pulcher/secureMoodTracker/Assests/20190905_112706.jpg

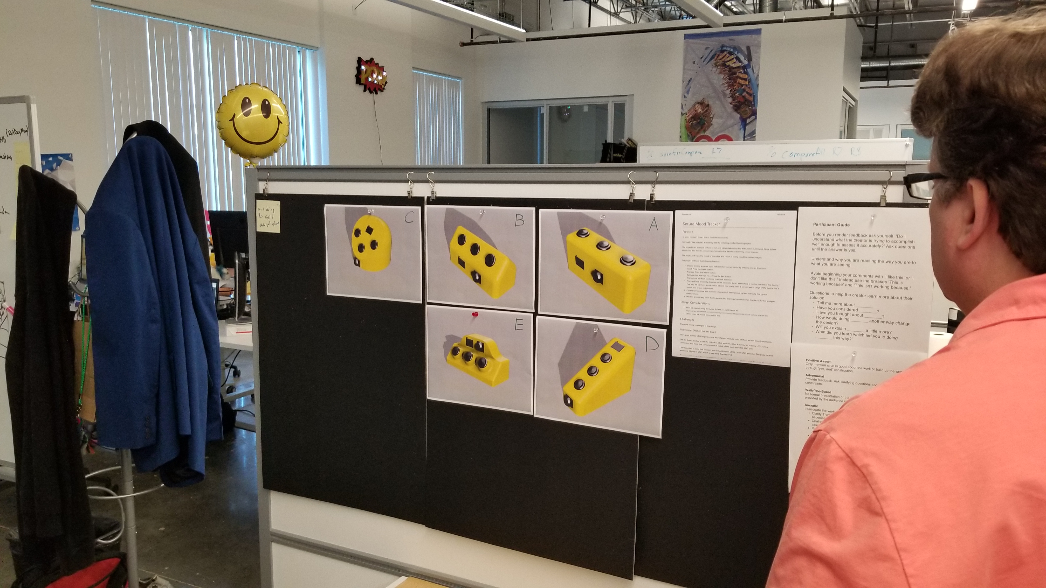
Assests/20190905_112706.jpg
