pulcher/secureMoodTracker/Assests/20190905_112857.jpg

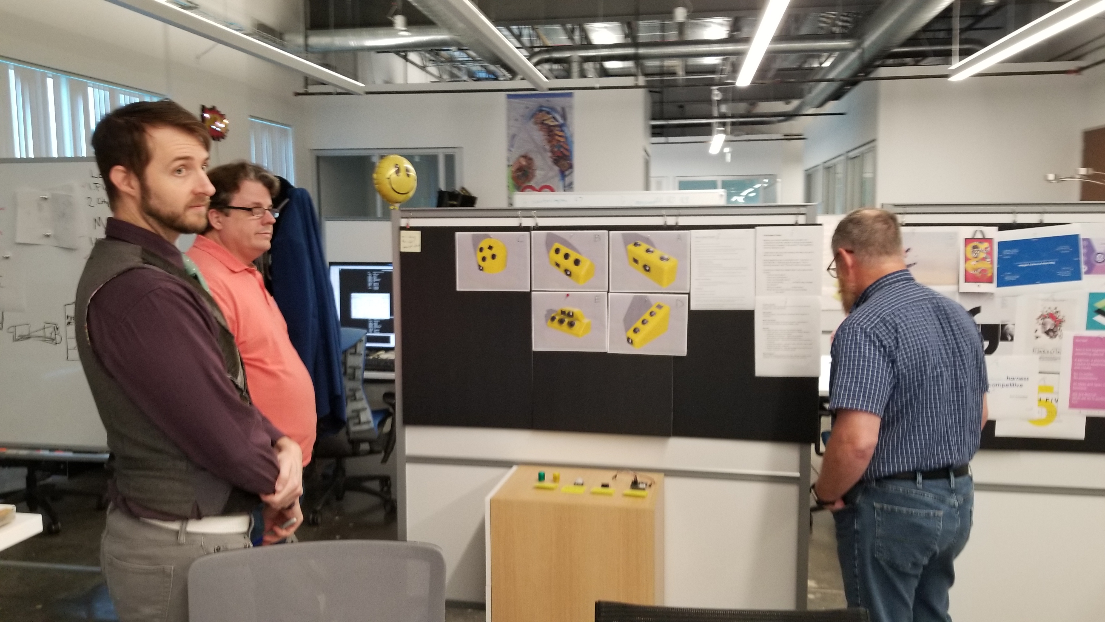
Assests/20190905_112857.jpg
