pulcher/secureMoodTracker/Assests/20190905_112900.jpg

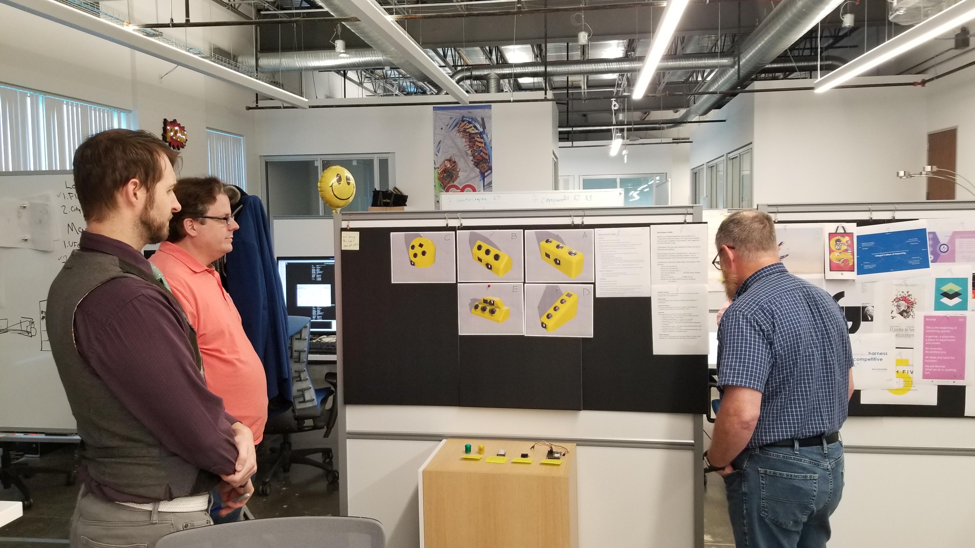
Assests/20190905_112900.jpg
