pulcher/secureMoodTracker/Assests/access-token-copy-token.jpg

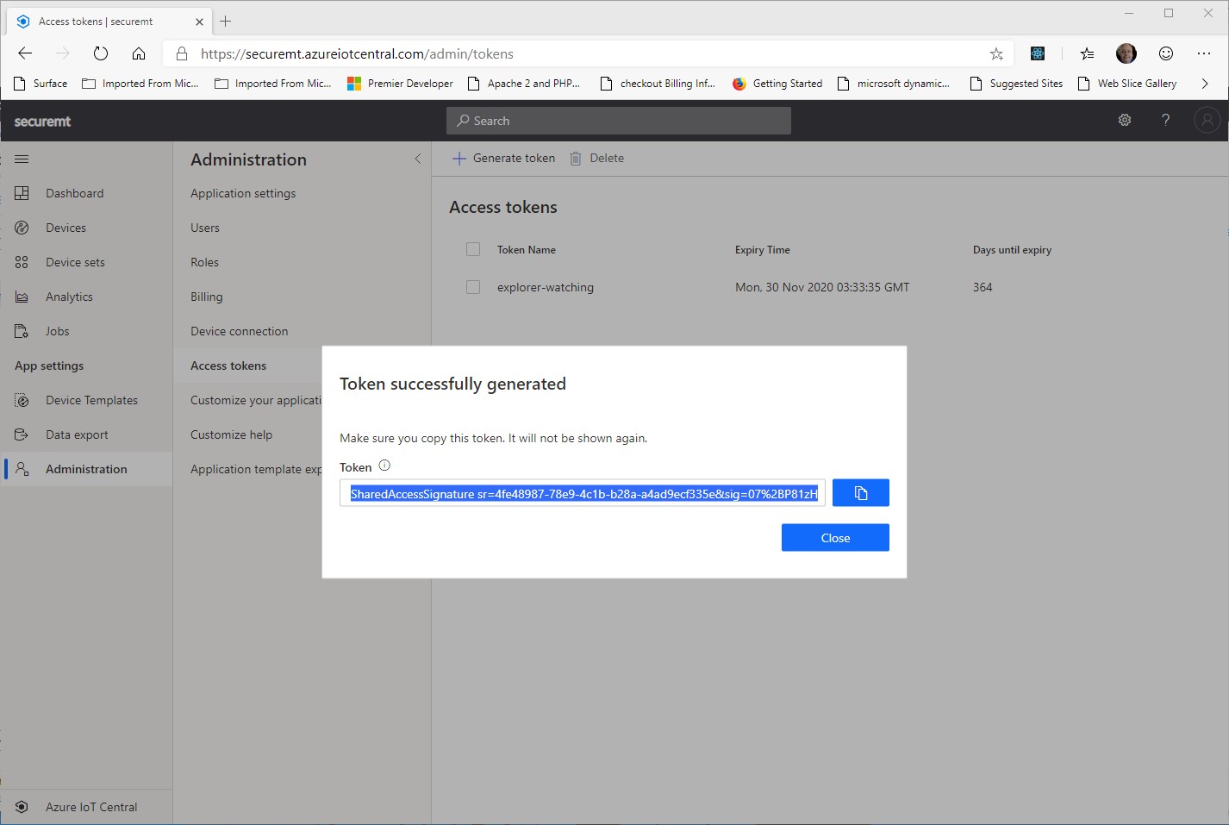
Assests/access-token-copy-token.jpg
