pulcher/secureMoodTracker/Assests/access-token-using-token.jpg

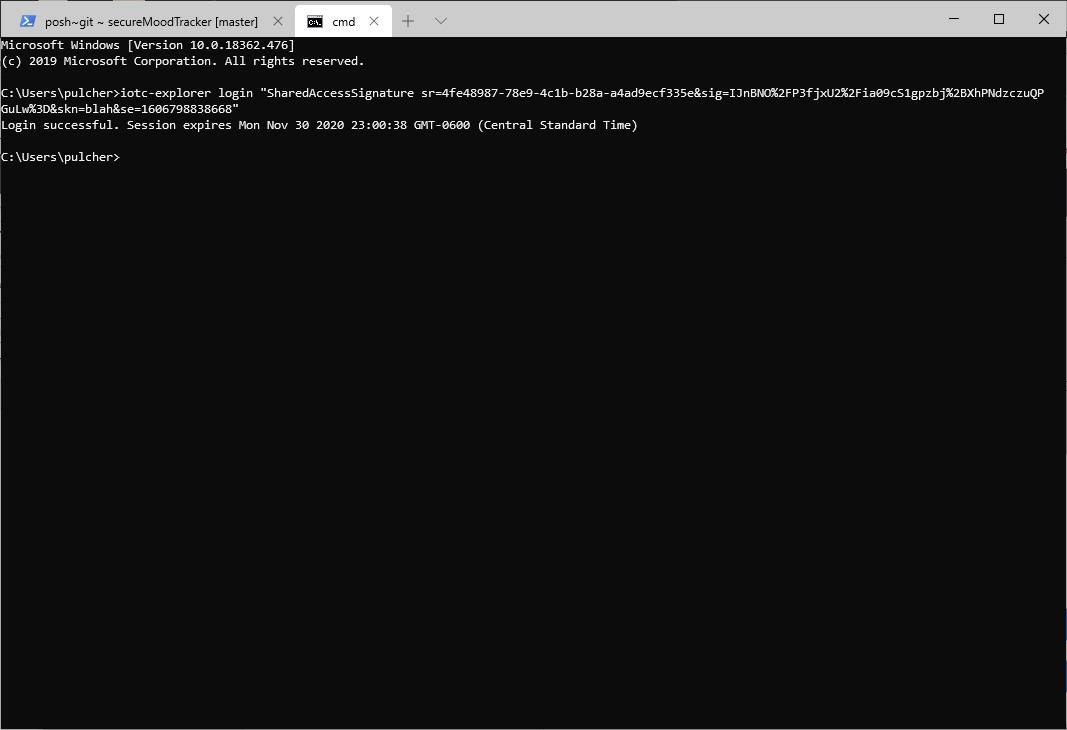
Assests/access-token-using-token.jpg
