pulcher/secureMoodTracker/Assests/adafruit mini arcade button v4.png

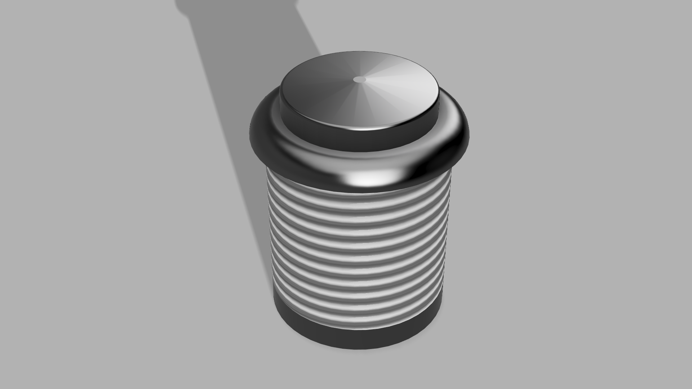
Assests/adafruit mini arcade button v4.png
