pulcher/secureMoodTracker/Assests/azsphere-login.jpg

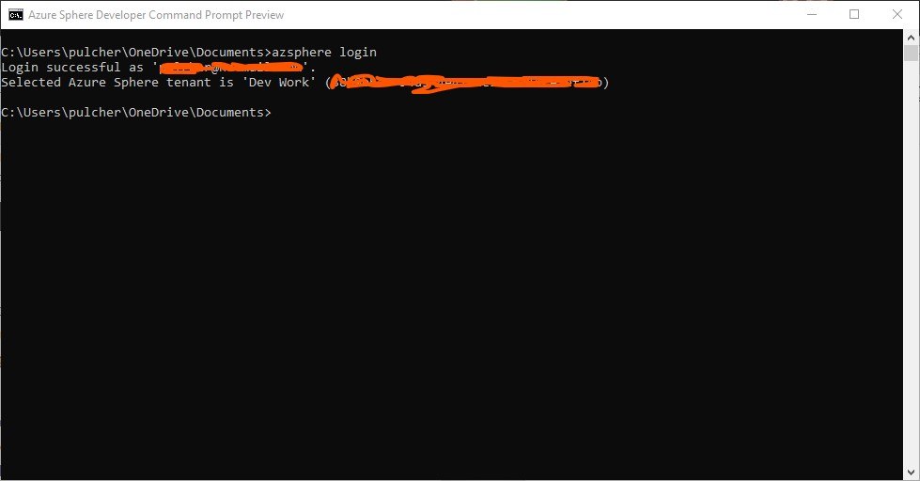
Assests/azsphere-login.jpg
