pulcher/secureMoodTracker/Assests/azsphere-show-attached.jpg

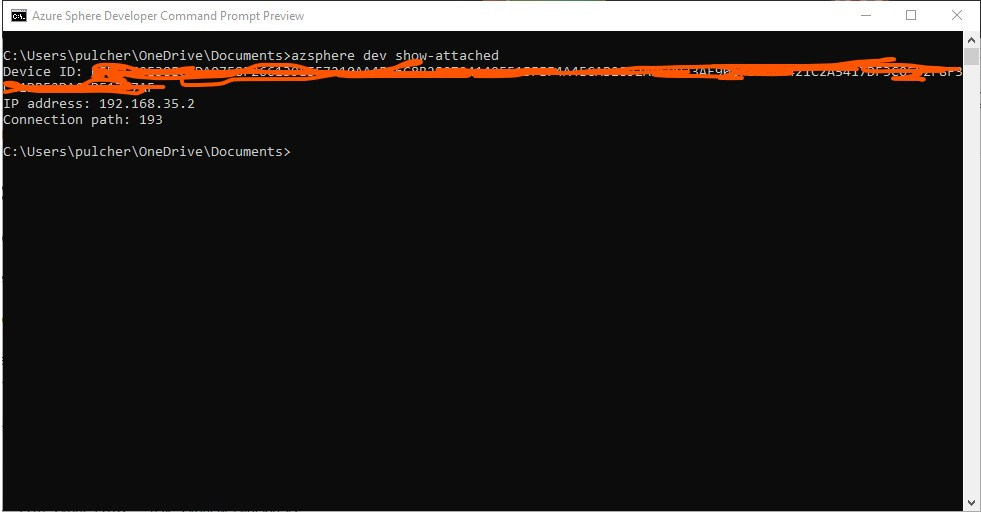
Assests/azsphere-show-attached.jpg
