pulcher/secureMoodTracker/Assests/azure-free-account.jpg

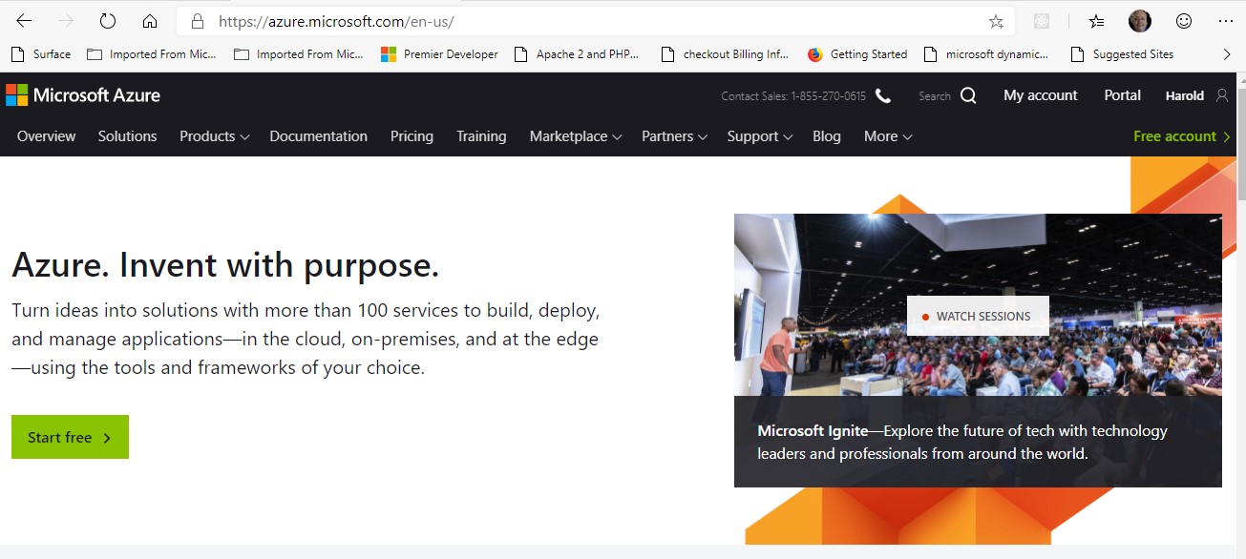
Assests/azure-free-account.jpg
