pulcher/secureMoodTracker/Assests/breadboard v1.png

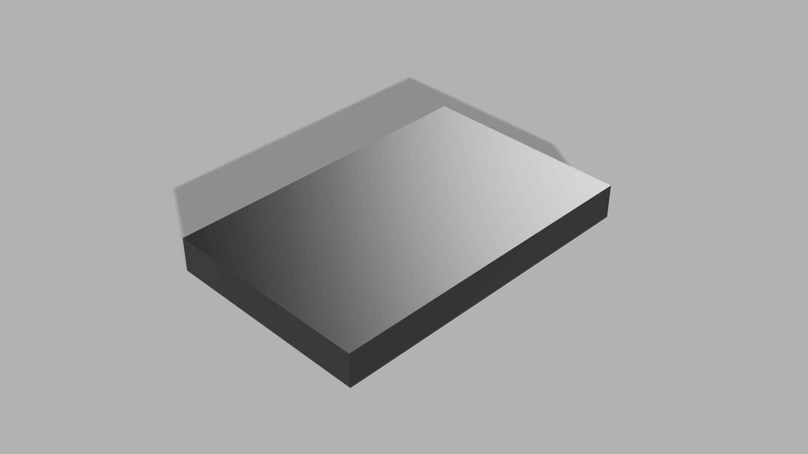
Assests/breadboard v1.png
