pulcher/secureMoodTracker/Assests/button riser v4.png

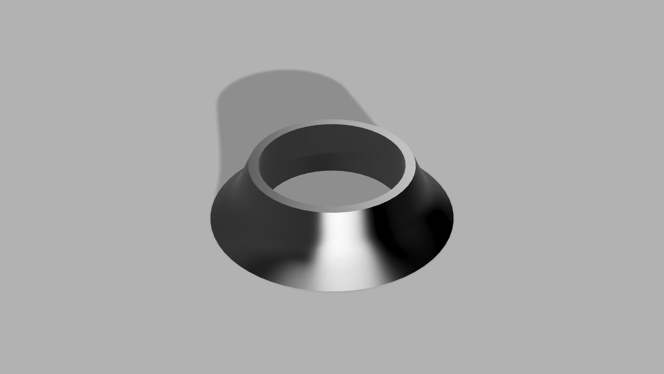
Assests/button riser v4.png
