pulcher/secureMoodTracker/Assests/button-timer-handler.jpg

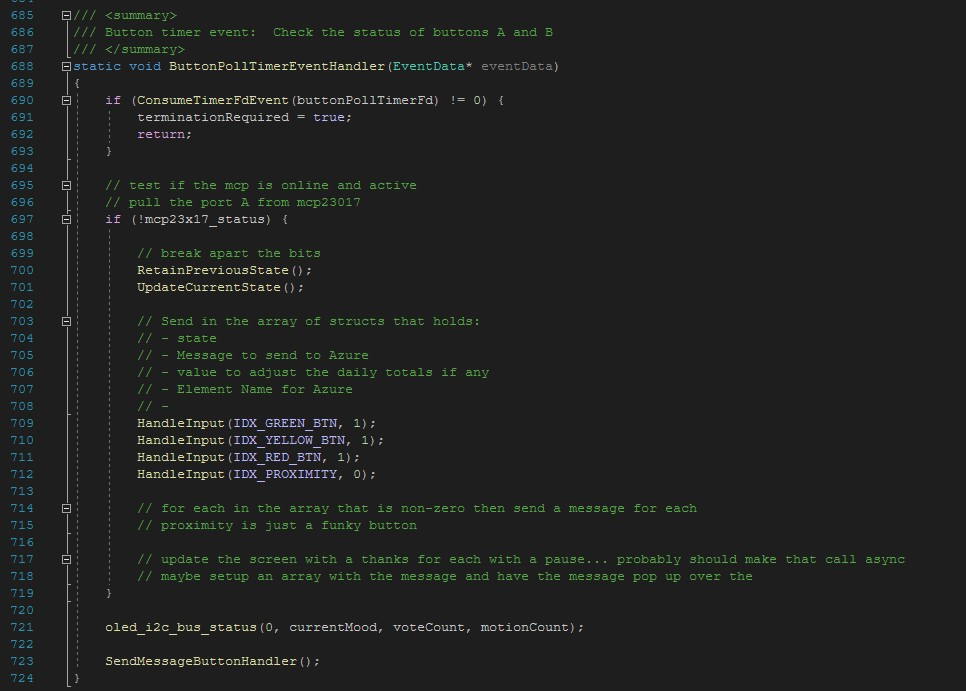
Assests/button-timer-handler.jpg
