pulcher/secureMoodTracker/Assests/cover-photo.jpg

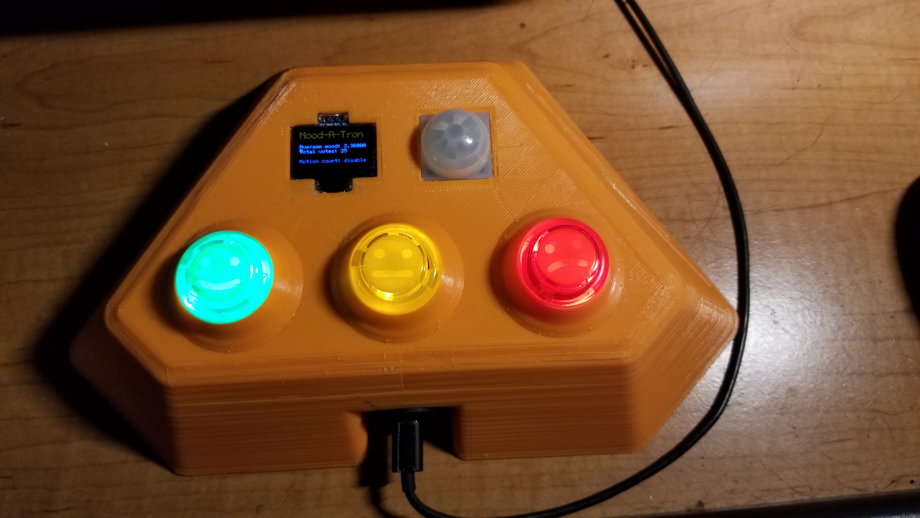
Assests/cover-photo.jpg
