pulcher/secureMoodTracker/Assests/dashboard-device-templates-edit-event.jpg

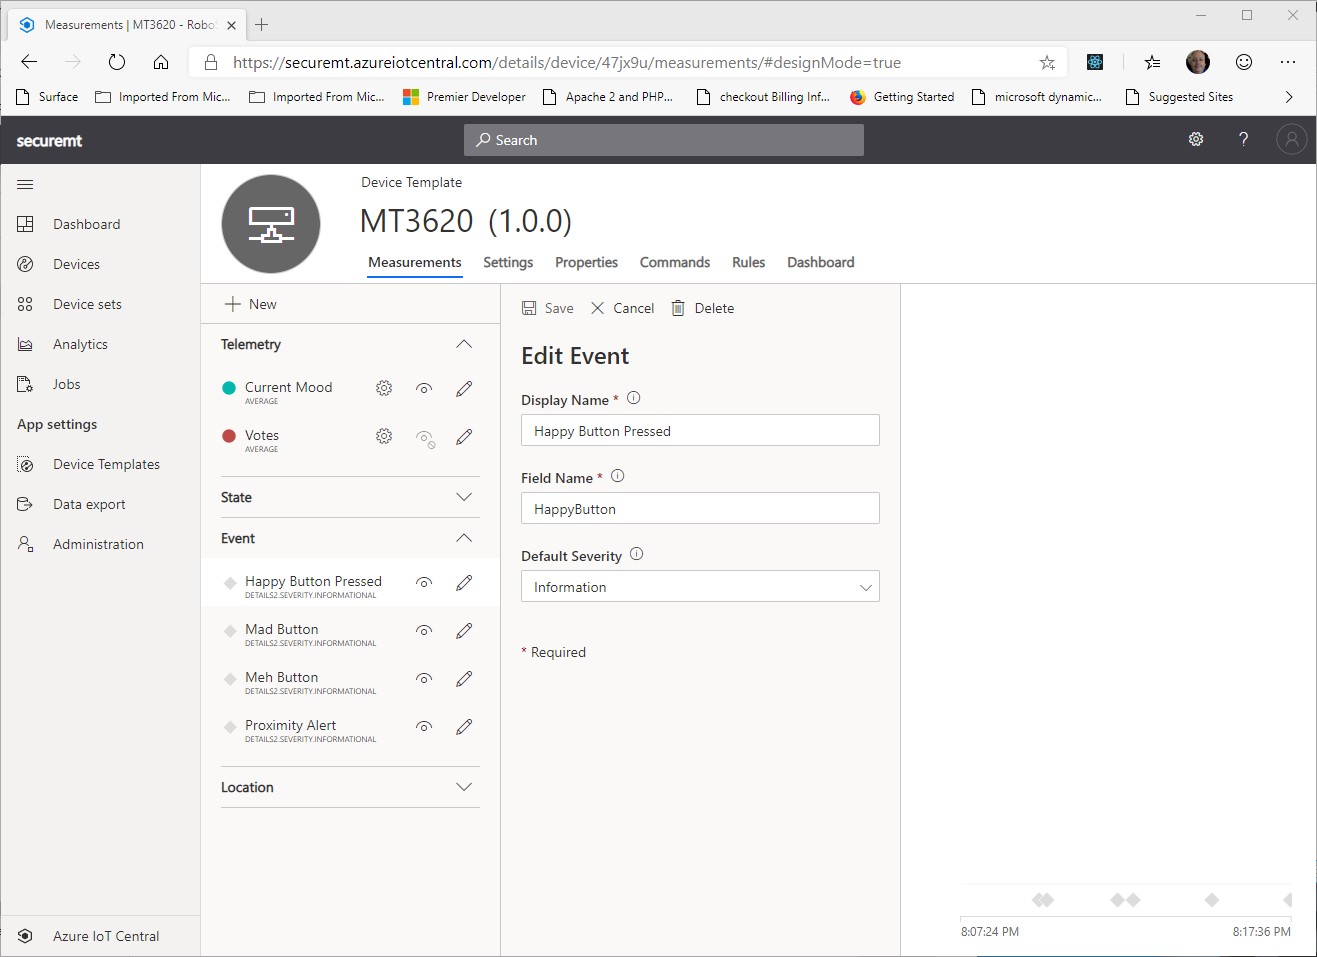
Assests/dashboard-device-templates-edit-event.jpg
