pulcher/secureMoodTracker/Assests/dashboard-device-templates-edit-telemetry.jpg

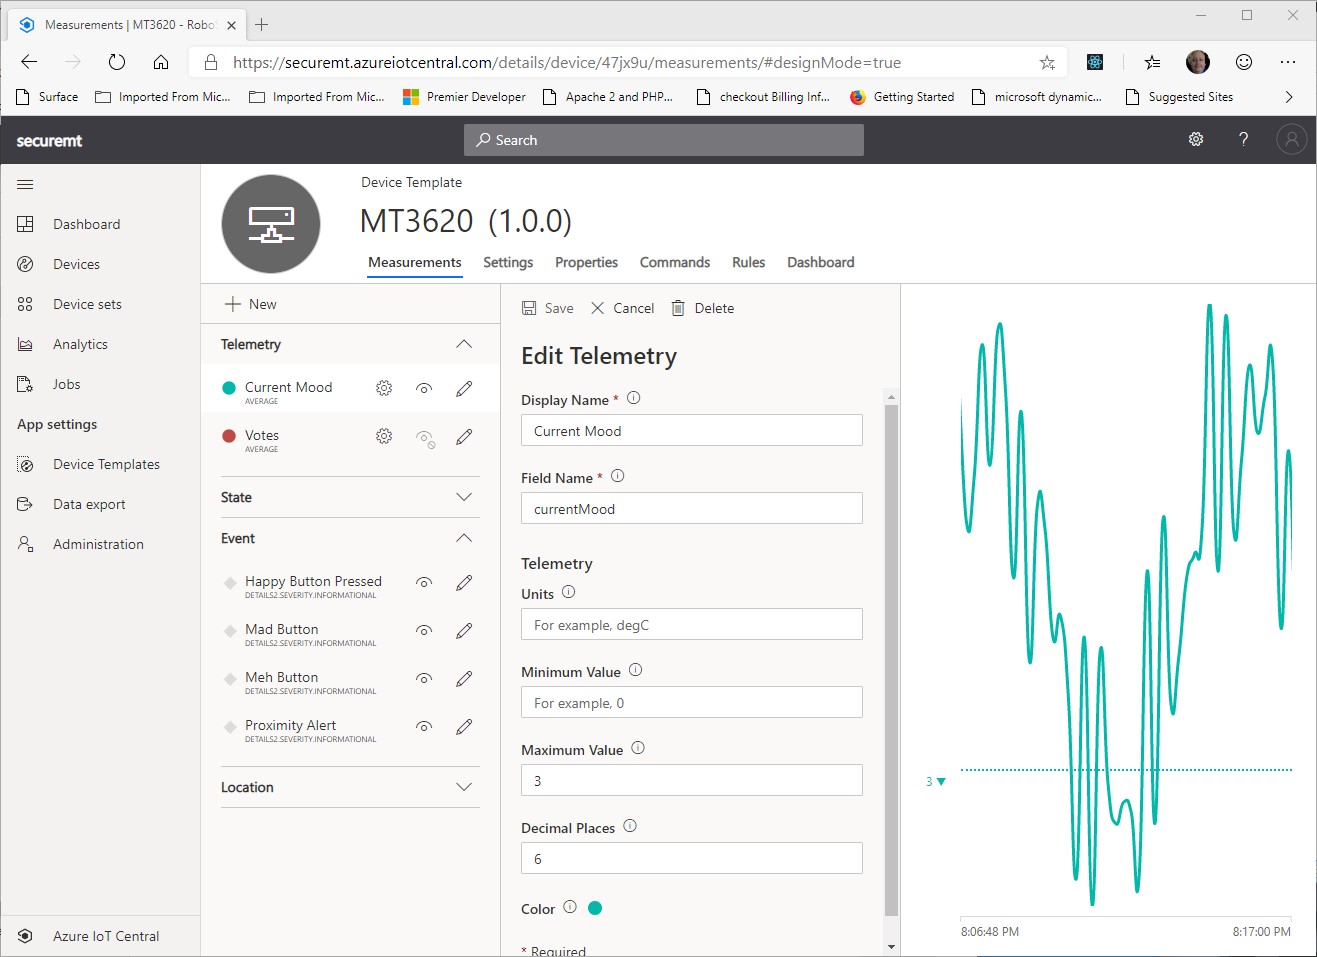
Assests/dashboard-device-templates-edit-telemetry.jpg
