pulcher/secureMoodTracker/Assests/dashboard-device-templates-edit.jpg

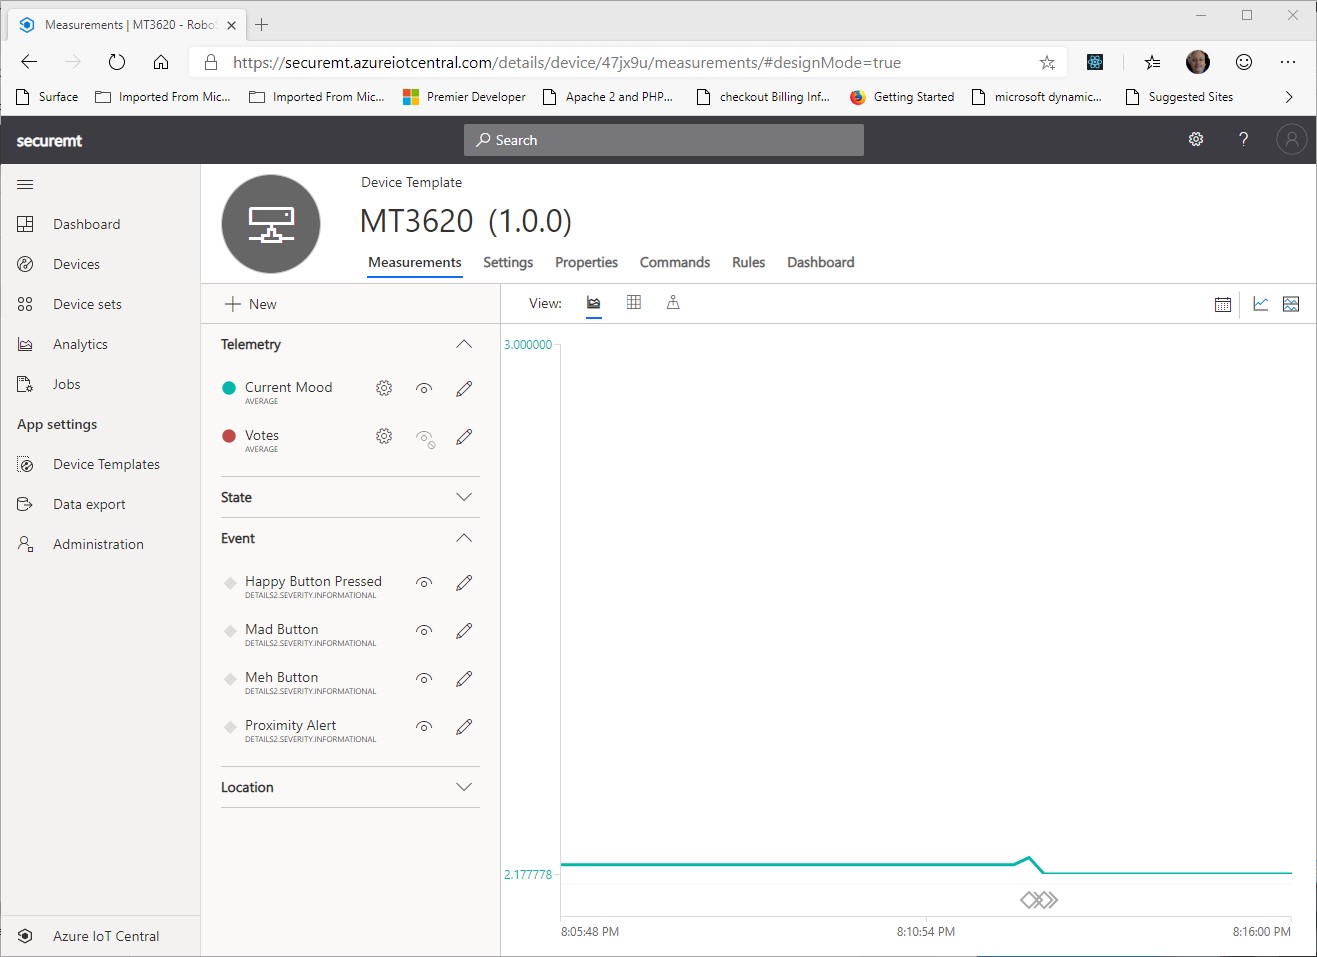
Assests/dashboard-device-templates-edit.jpg
