pulcher/secureMoodTracker/Assests/dashboard-device-templates.jpg

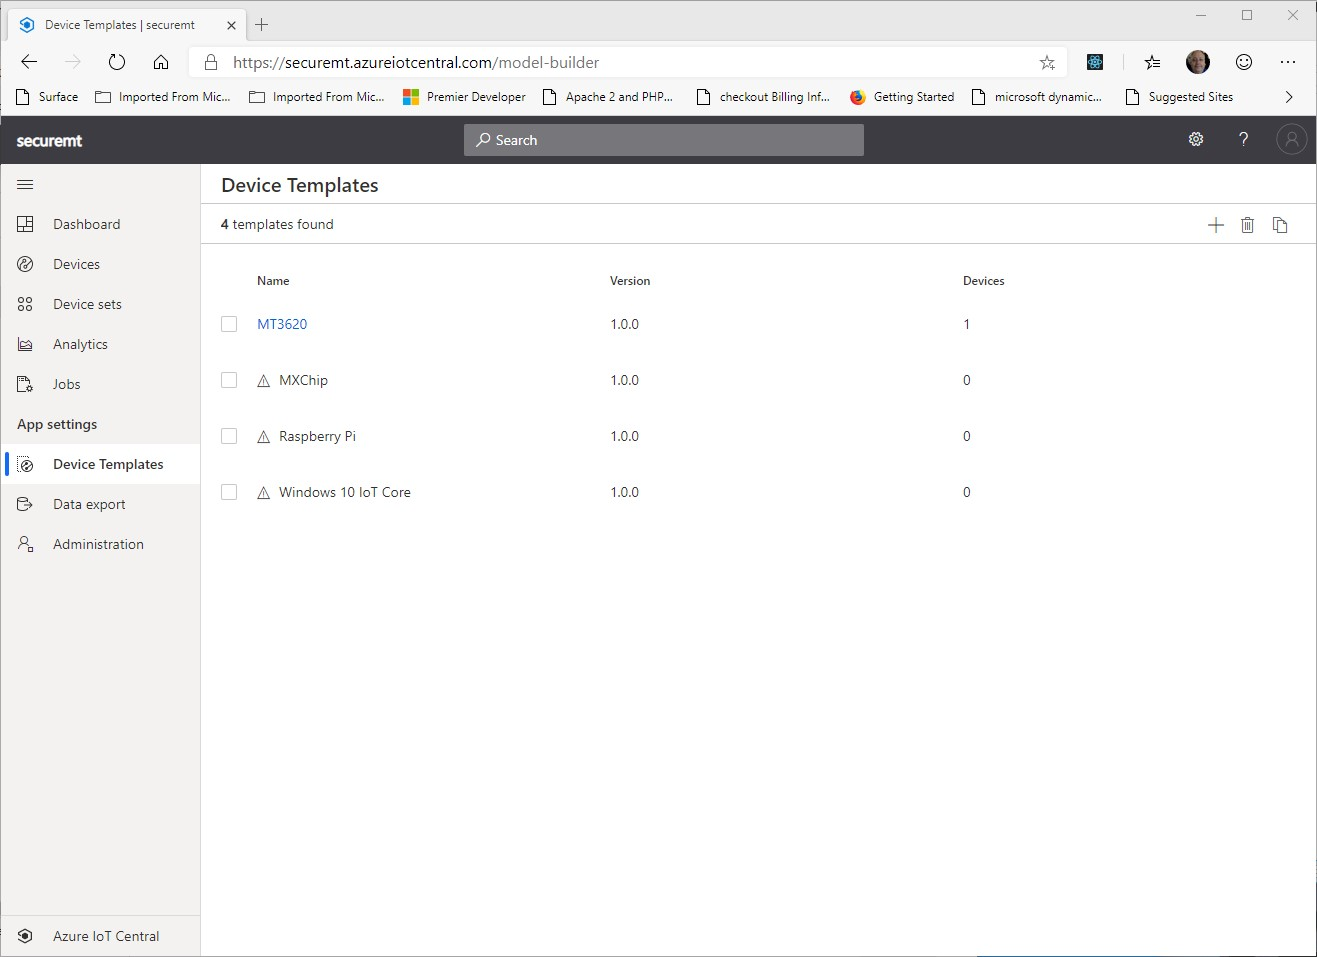
Assests/dashboard-device-templates.jpg
