pulcher/secureMoodTracker/Assests/dashboard-main-events.jpg

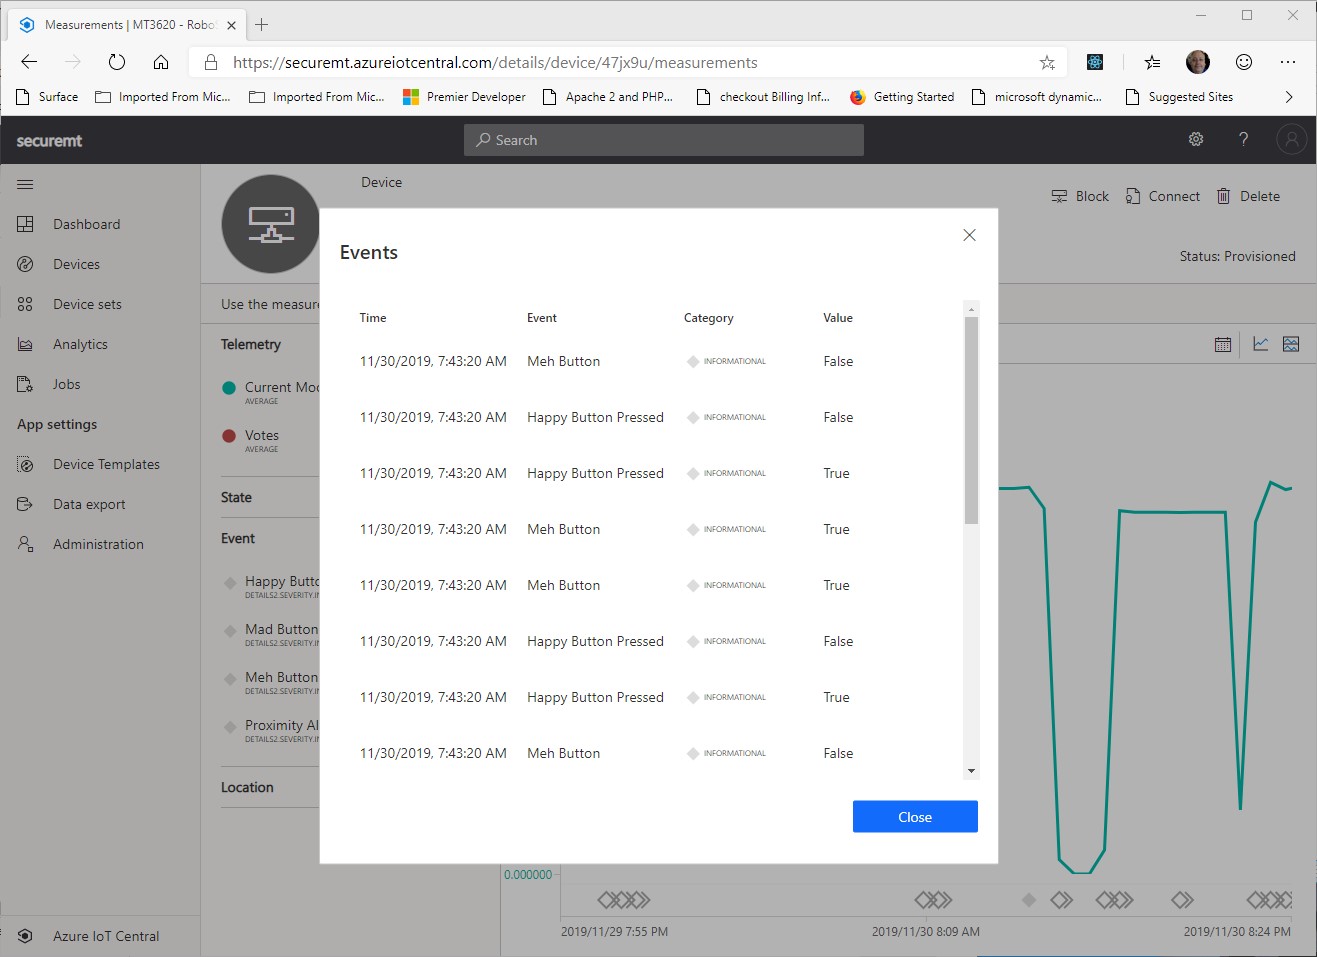
Assests/dashboard-main-events.jpg
