pulcher/secureMoodTracker/Assests/dashboard-main.jpg

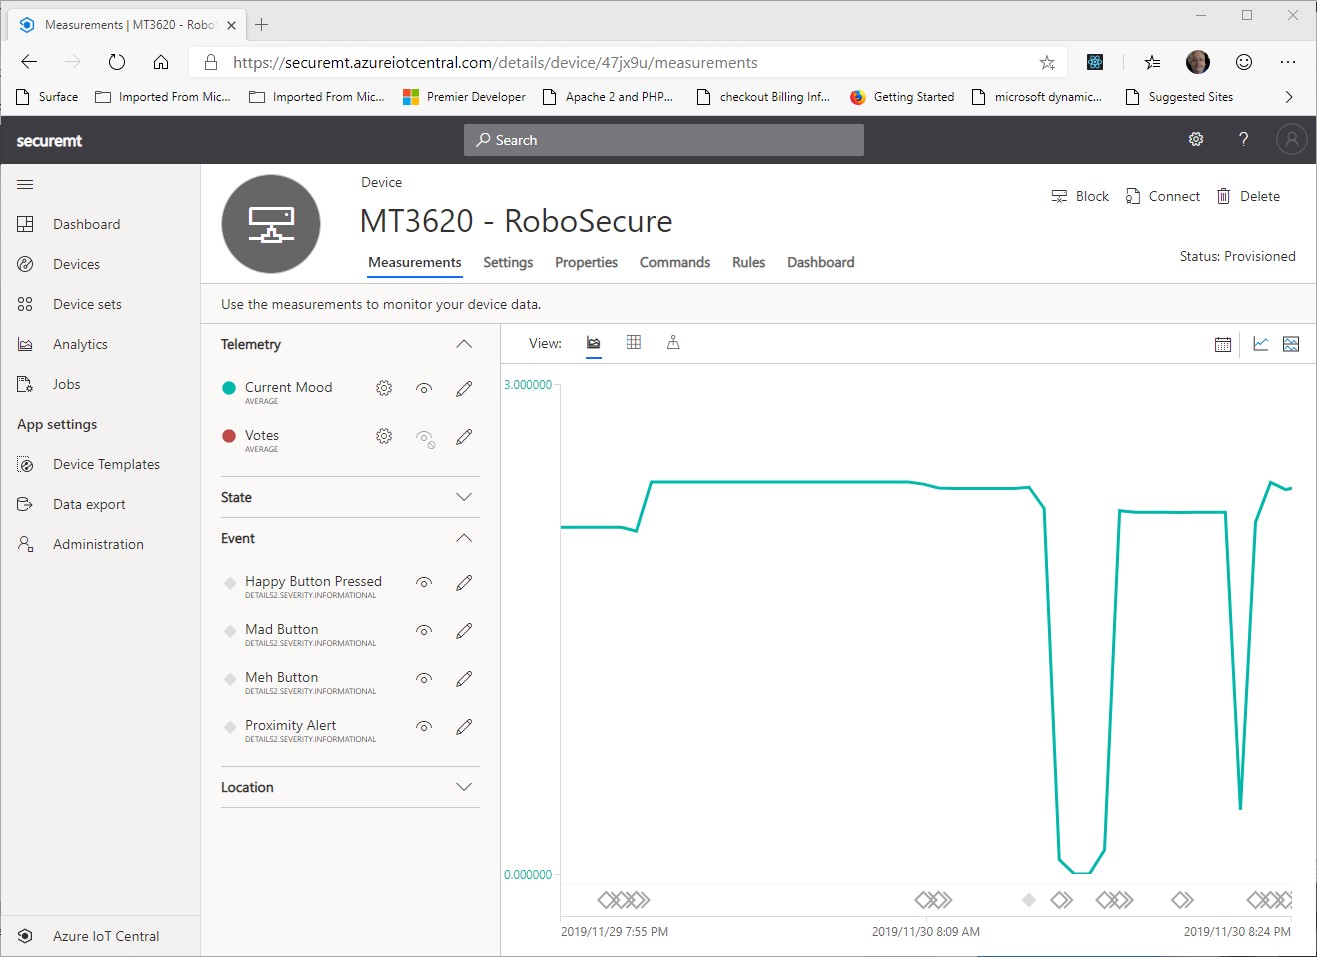
Assests/dashboard-main.jpg
