pulcher/secureMoodTracker/Assests/emoji v2.png

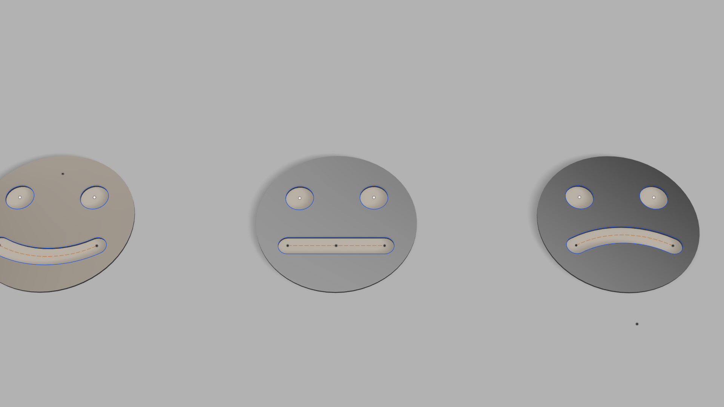
Assests/emoji v2.png
