pulcher/secureMoodTracker/Assests/handle-input.jpg

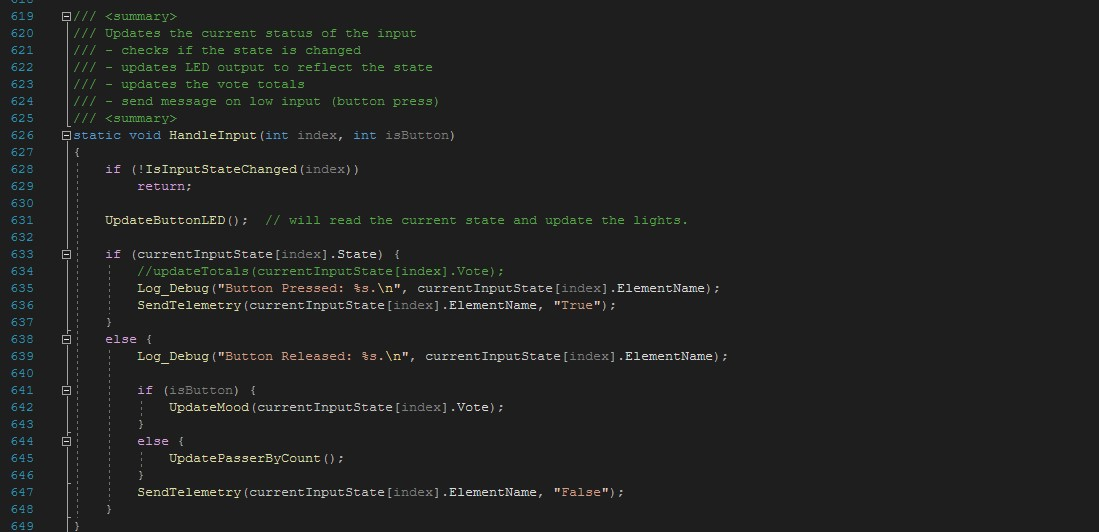
Assests/handle-input.jpg
