pulcher/secureMoodTracker/Assests/main-loop.jpg

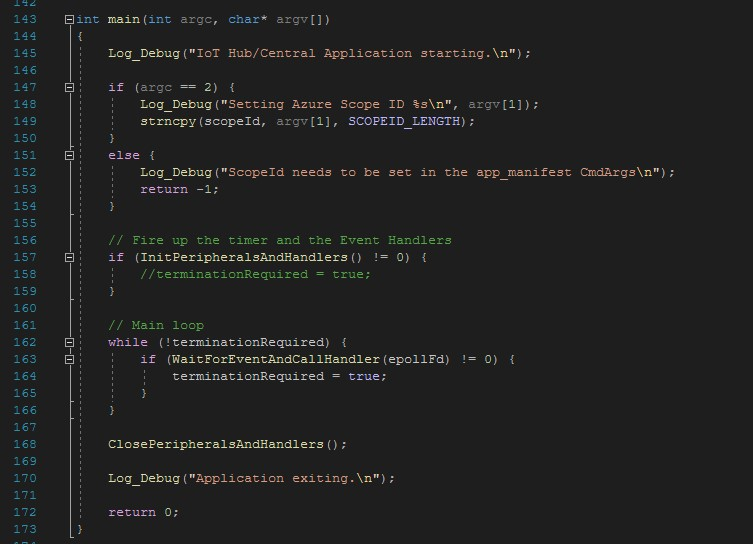
Assests/main-loop.jpg
