pulcher/secureMoodTracker/Assests/main-wait-end.jpg

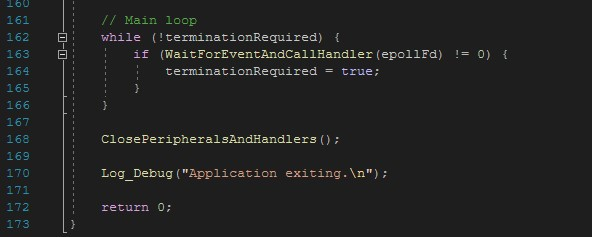
Assests/main-wait-end.jpg
