pulcher/secureMoodTracker/Assests/mcp23017 breakout v1.png

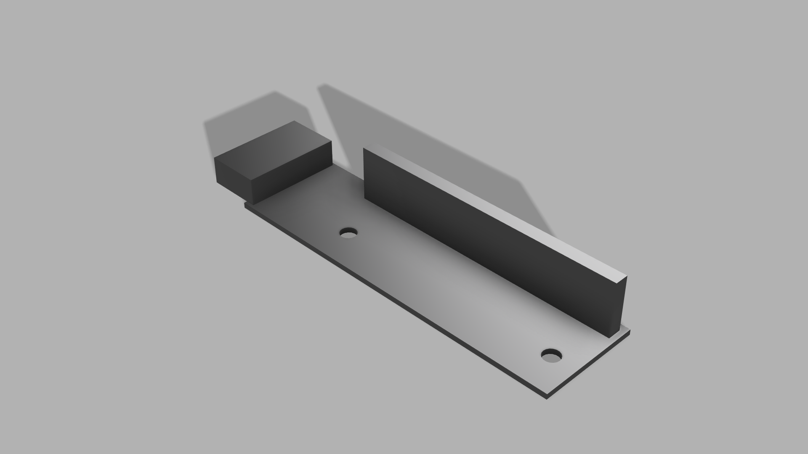
Assests/mcp23017 breakout v1.png
