pulcher/secureMoodTracker/Assests/mcp23017-module-isojpg.jpg

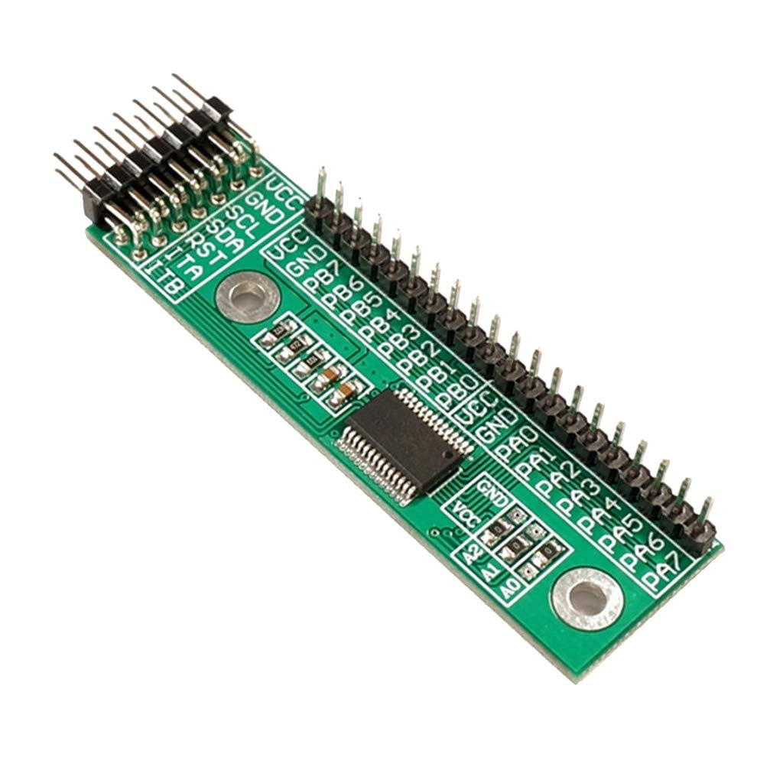
Assests/mcp23017-module-isojpg.jpg
