pulcher/secureMoodTracker/Assests/MT3630 v2.png

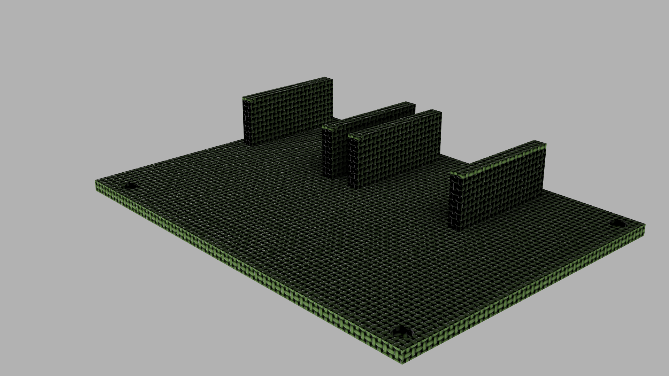
Assests/MT3630 v2.png
