pulcher/secureMoodTracker/Assests/npn-switch-led.png

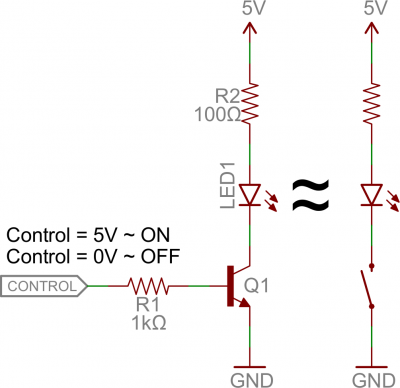
Assests/npn-switch-led.png
