pulcher/secureMoodTracker/Assests/oled display v2.png

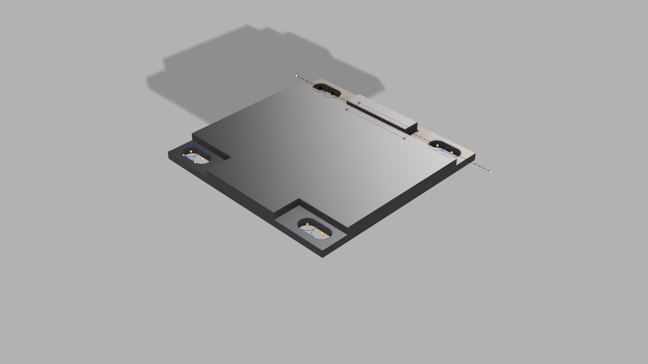
Assests/oled display v2.png
