pulcher/secureMoodTracker/Assests/PIR motion detector v1.png

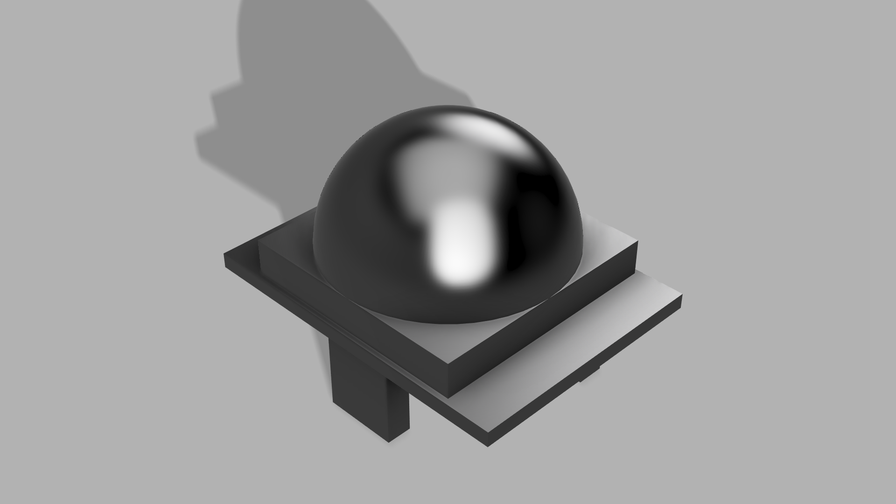
Assests/PIR motion detector v1.png
