pulcher/secureMoodTracker/Assests/send-button-message.jpg

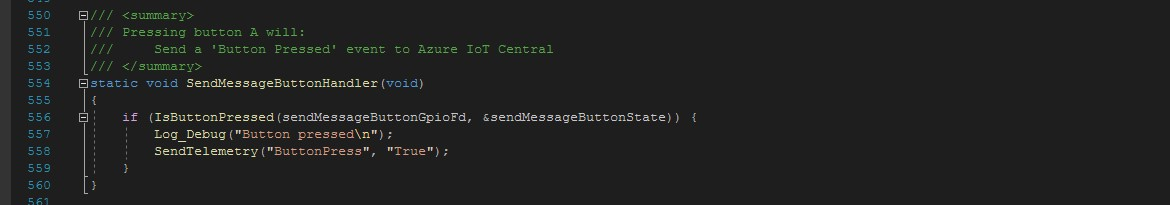
Assests/send-button-message.jpg
