pulcher/secureMoodTracker/Assests/send-telemetry.jpg

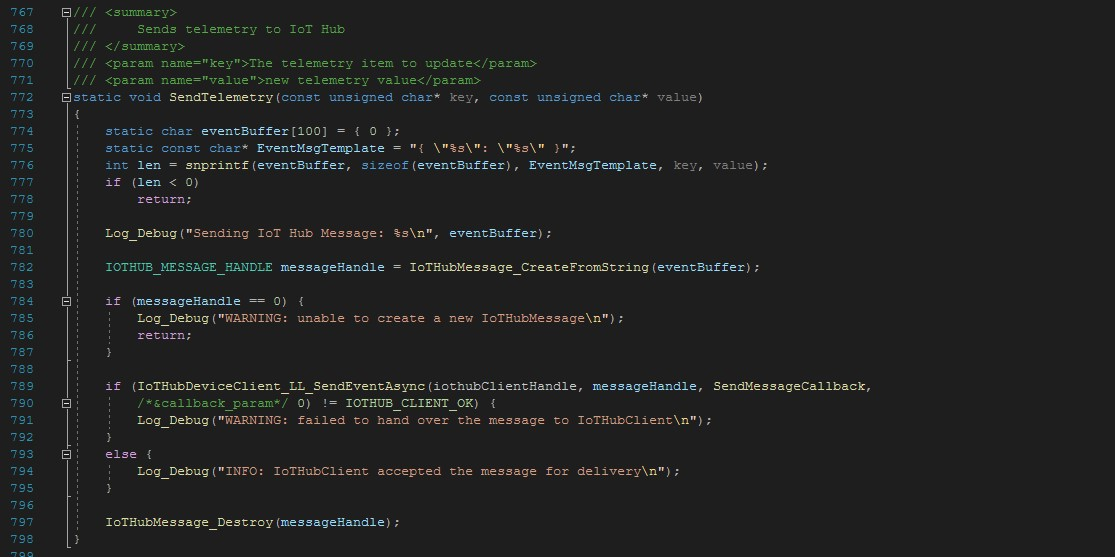
Assests/send-telemetry.jpg
