pulcher/secureMoodTracker/Assests/update-and-retain-state.jpg

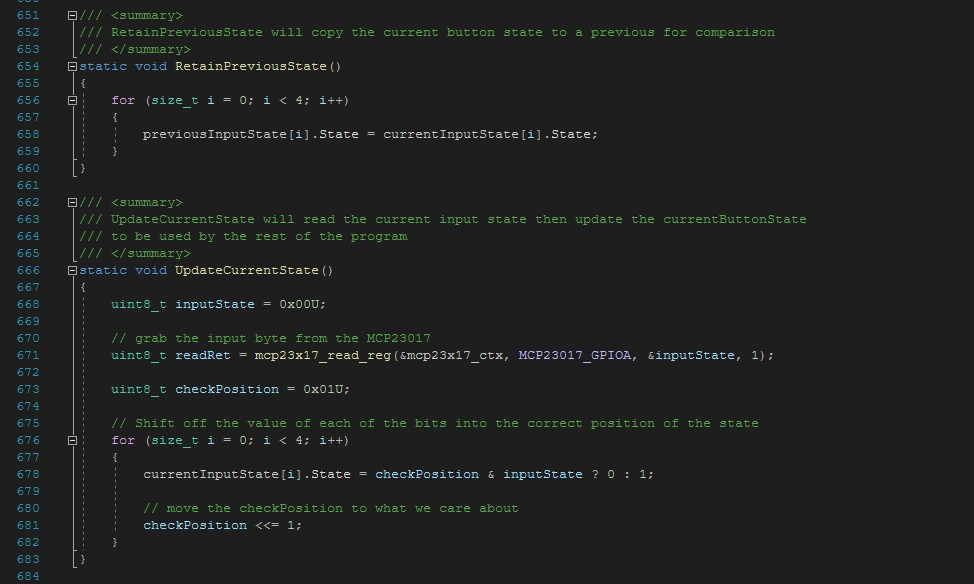
Assests/update-and-retain-state.jpg
