pulcher/secureMoodTracker/Assests/update-mood-and-motion.jpg

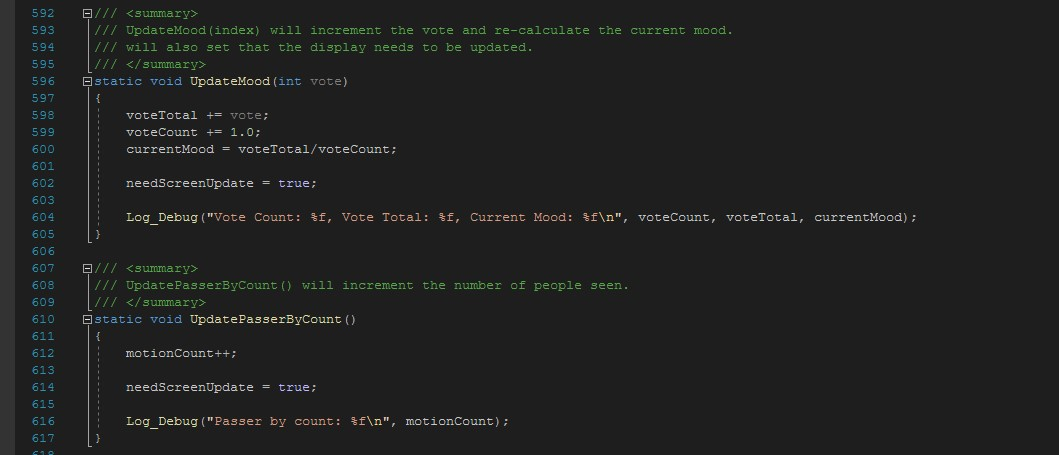
Assests/update-mood-and-motion.jpg
