pulcher/secureMoodTracker/Case Designs/a v3.png

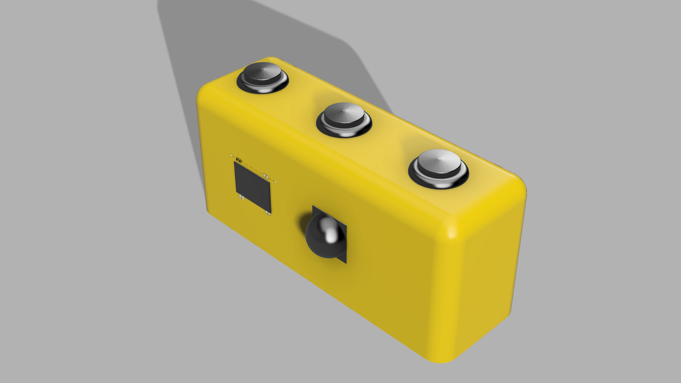
Case Designs/a v3.png
