pulcher/secureMoodTracker/Case Designs/e v1.png

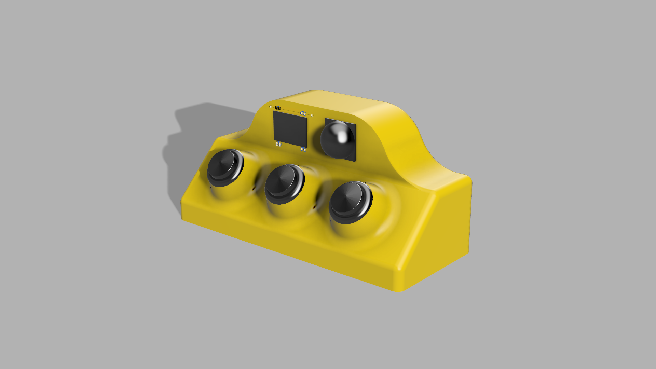
Case Designs/e v1.png
