pulcher/secureMoodTracker/Case Designs/e-draft v2.png

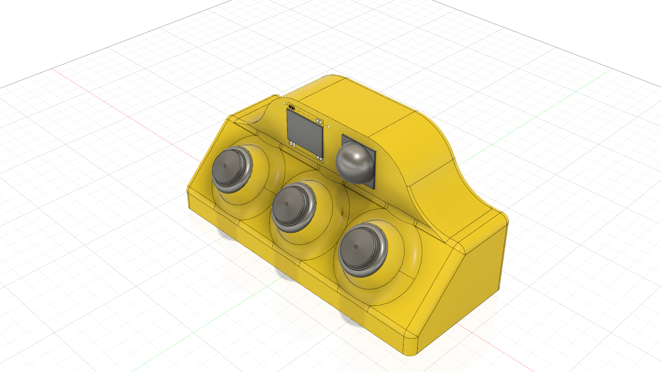
Case Designs/e-draft v2.png
