pulcher/secureMoodTracker/Case Designs/f -1v1.png

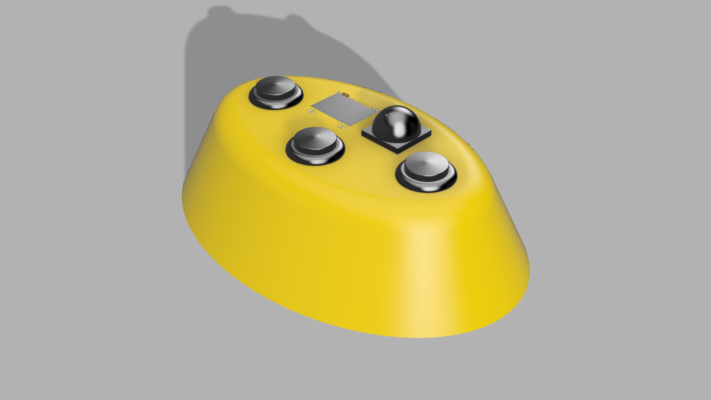
Case Designs/f -1v1.png
