pulcher/secureMoodTracker/Case Designs/g v2.png

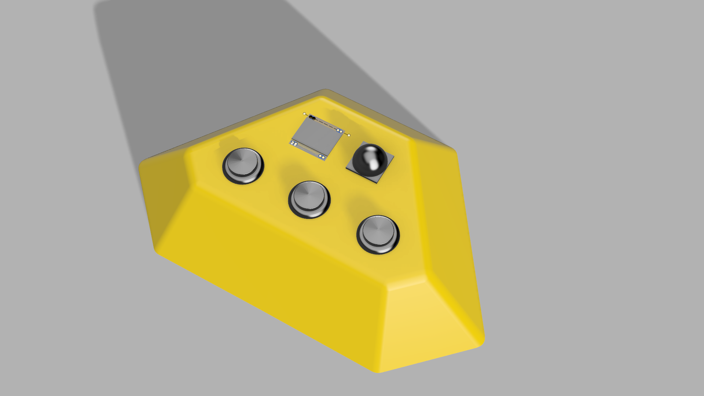
Case Designs/g v2.png
