pulcher/secureMoodTracker/Assests/oled-operation.jpg

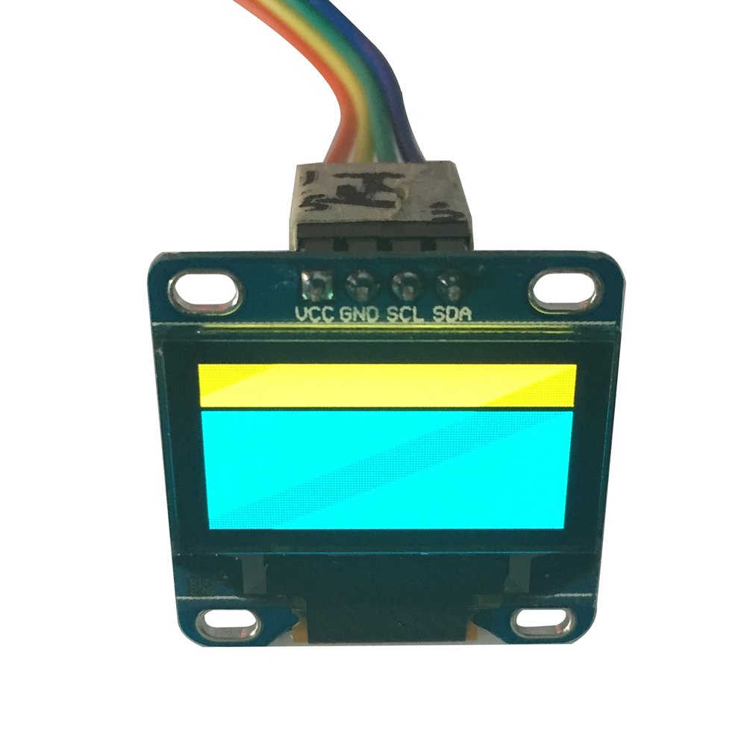
Assests/oled-operation.jpg
