pulcher/secureMoodTracker/secureMoodTracker/i2c.c

/*
 *  Some of the code in this file was copied from ST Micro.  Below is their required information.
 *
 * @attention
 *
 * <h2><center>&copy; COPYRIGHT(c) 2018 STMicroelectronics</center></h2>
 *
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
 * THIS SOFTWARE IS PROVIDED BY THE COPYRIGHT HOLDERS AND CONTRIBUTORS "AS IS"
 * AND ANY EXPRESS OR IMPLIED WARRANTIES, INCLUDING, BUT NOT LIMITED TO, THE
 * ARE DISCLAIMED. IN NO EVENT SHALL THE COPYRIGHT HOLDER OR CONTRIBUTORS BE
 * LIABLE FOR ANY DIRECT, INDIRECT, INCIDENTAL, SPECIAL, EXEMPLARY, OR
 * CONSEQUENTIAL DAMAGES (INCLUDING, BUT NOT LIMITED TO, PROCUREMENT OF
 * SUBSTITUTE GOODS OR SERVICES; LOSS OF USE, DATA, OR PROFITS; OR BUSINESS
 * INTERRUPTION) HOWEVER CAUSED AND ON ANY THEORY OF LIABILITY, WHETHER IN
 * CONTRACT, STRICT LIABILITY, OR TORT (INCLUDING NEGLIGENCE OR OTHERWISE)
 * ARISING IN ANY WAY OUT OF THE USE OF THIS SOFTWARE, EVEN IF ADVISED OF THE
 * POSSIBILITY OF SUCH DAMAGE.
 *
 */

#include <errno.h>
#include <signal.h>
#include <stdbool.h>
#include <stdio.h>
#include <math.h>
#include <stdlib.h>

// applibs_versions.h defines the API struct versions to use for applibs APIs.
#include "applibs_versions.h"

#include <applibs/log.h>
#include <applibs/i2c.h>

#include "mt3620_avnet_dev.h"
#include "deviceTwin.h"
#include "azure_iot_utilities.h"
#include "build_options.h"
#include "i2c.h"
#include "lsm6dso_reg.h"
#include "lps22hh_reg.h"
#include "mcp23x17.h"

/* Private variables ---------------------------------------------------------*/
static axis3bit16_t data_raw_acceleration;
static axis3bit16_t data_raw_angular_rate;
static axis3bit16_t raw_angular_rate_calibration;
static axis1bit32_t data_raw_pressure;
static axis1bit16_t data_raw_temperature;
static float acceleration_mg[3];
static float angular_rate_dps[3];
static float lsm6dsoTemperature_degC;
static float pressure_hPa;
static float lps22hhTemperature_degC;

static uint8_t whoamI, rst;
static int accelTimerFd = -1;
const uint8_t lsm6dsOAddress = LSM6DSO_ADDRESS;     // Addr = 0x6A
lsm6dso_ctx_t dev_ctx;
lps22hh_ctx_t pressure_ctx;
mcp23x17_ctx_t mcp23x17_ctx;

float altitude;

// Status variables
uint8_t lsm6dso_status = 1;
uint8_t lps22hh_status = 1;
uint8_t mcp23x17_status = 1;
uint8_t RTCore_status = 1;

//Extern variables
int i2cFd = -1;
extern int epollFd;
extern volatile sig_atomic_t terminationRequired;

//Private functions

// Routines to read/write to the LSM6DSO device
static int32_t platform_write(int *fD, uint8_t reg, uint8_t *bufp, uint16_t len);
static int32_t platform_read(int *fD, uint8_t reg, uint8_t *bufp, uint16_t len);

// Routines to read/write to the LPS22HH device connected to the LSM6DSO sensor hub
static int32_t lsm6dso_write_lps22hh_cx(void* ctx, uint8_t reg, uint8_t* data, uint16_t len);
static int32_t lsm6dso_read_lps22hh_cx(void* ctx, uint8_t reg, uint8_t* data, uint16_t len);

// Routines to read/write to the MCP23X17 device connected to I2C
static uint8_t mcp23x17_read_cx(mcp23x17_ctx_t* ctx, uint8_t reg, uint8_t* data, uint8_t len);
static uint8_t mcp23x17_write_cx(mcp23x17_ctx_t* ctx, uint8_t reg, uint8_t* data, uint8_t len);

/// <summary>
///     Sleep for delayTime ms
/// </summary>
void HAL_Delay(int delayTime) {
	struct timespec ts;
	ts.tv_sec = 0;
	ts.tv_nsec = delayTime * 10000;
	nanosleep(&ts, NULL);
}

/// <summary>
///     Print latest data from on-board sensors.
/// </summary>
void AccelTimerEventHandler(EventData *eventData)
{
	uint8_t reg;
	lps22hh_reg_t lps22hhReg;

#if (defined(IOT_CENTRAL_APPLICATION) || defined(IOT_HUB_APPLICATION))
	static bool firstPass = true;
#endif
	// Consume the event.  If we don't do this we'll come right back
	// to process the same event again
	if (ConsumeTimerFdEvent(accelTimerFd) != 0) {
		terminationRequired = true;
		return;
	}

	// Read the sensors on the lsm6dso device

	//Read output only if new xl value is available
	lsm6dso_xl_flag_data_ready_get(&dev_ctx, &reg);
	if (reg)
	{
		// Read acceleration field data
		memset(data_raw_acceleration.u8bit, 0x00, 3 * sizeof(int16_t));
		lsm6dso_acceleration_raw_get(&dev_ctx, data_raw_acceleration.u8bit);

		acceleration_mg[0] = lsm6dso_from_fs4_to_mg(data_raw_acceleration.i16bit[0]);
		acceleration_mg[1] = lsm6dso_from_fs4_to_mg(data_raw_acceleration.i16bit[1]);
		acceleration_mg[2] = lsm6dso_from_fs4_to_mg(data_raw_acceleration.i16bit[2]);

		Log_Debug("\nLSM6DSO: Acceleration [mg]  : %.4lf, %.4lf, %.4lf\n",
			acceleration_mg[0], acceleration_mg[1], acceleration_mg[2]);
	}

	lsm6dso_gy_flag_data_ready_get(&dev_ctx, &reg);
	if (reg)
	{
		// Read angular rate field data
		memset(data_raw_angular_rate.u8bit, 0x00, 3 * sizeof(int16_t));
		lsm6dso_angular_rate_raw_get(&dev_ctx, data_raw_angular_rate.u8bit);

		// Before we store the mdps values subtract the calibration data we captured at startup.
		angular_rate_dps[0] = (lsm6dso_from_fs2000_to_mdps(data_raw_angular_rate.i16bit[0] - raw_angular_rate_calibration.i16bit[0])) / 1000.0;
		angular_rate_dps[1] = (lsm6dso_from_fs2000_to_mdps(data_raw_angular_rate.i16bit[1] - raw_angular_rate_calibration.i16bit[1])) / 1000.0;
		angular_rate_dps[2] = (lsm6dso_from_fs2000_to_mdps(data_raw_angular_rate.i16bit[2] - raw_angular_rate_calibration.i16bit[2])) / 1000.0;

		Log_Debug("LSM6DSO: Angular rate [dps] : %4.2f, %4.2f, %4.2f\r\n",
			angular_rate_dps[0], angular_rate_dps[1], angular_rate_dps[2]);

	}

	lsm6dso_temp_flag_data_ready_get(&dev_ctx, &reg);
	if (reg)
	{
		// Read temperature data
		memset(data_raw_temperature.u8bit, 0x00, sizeof(int16_t));
		lsm6dso_temperature_raw_get(&dev_ctx, data_raw_temperature.u8bit);
		lsm6dsoTemperature_degC = lsm6dso_from_lsb_to_celsius(data_raw_temperature.i16bit);

		Log_Debug("LSM6DSO: Temperature1 [degC]: %.2f\r\n", lsm6dsoTemperature_degC);
	}

	// Read the sensors on the lsm6dso device

	lps22hh_read_reg(&pressure_ctx, LPS22HH_STATUS, (uint8_t *)&lps22hhReg, 1);

	//Read output only if new value is available

	if ((lps22hhReg.status.p_da == 1) && (lps22hhReg.status.t_da == 1))
	{
		memset(data_raw_pressure.u8bit, 0x00, sizeof(int32_t));
		lps22hh_pressure_raw_get(&pressure_ctx, data_raw_pressure.u8bit);

		pressure_hPa = lps22hh_from_lsb_to_hpa((uint32_t)data_raw_pressure.i32bit);

		memset(data_raw_temperature.u8bit, 0x00, sizeof(int16_t));
		lps22hh_temperature_raw_get(&pressure_ctx, data_raw_temperature.u8bit);
		lps22hhTemperature_degC = lps22hh_from_lsb_to_celsius(data_raw_temperature.i16bit);

		Log_Debug("LPS22HH: Pressure     [hPa] : %.2f\r\n", pressure_hPa);
		Log_Debug("LPS22HH: Temperature2 [degC]: %.2f\r\n", lps22hhTemperature_degC);
	}


	sensor_data.acceleration_mg[0] = acceleration_mg[0];
	sensor_data.acceleration_mg[1] = acceleration_mg[1];
	sensor_data.acceleration_mg[2] = acceleration_mg[2];
	sensor_data.angular_rate_dps[0] = angular_rate_dps[0];
	sensor_data.angular_rate_dps[1] = angular_rate_dps[1];
	sensor_data.angular_rate_dps[2] = angular_rate_dps[2];
	sensor_data.lsm6dsoTemperature_degC = lsm6dsoTemperature_degC;
	sensor_data.lps22hhpressure_hPa = pressure_hPa;
	sensor_data.lps22hhTemperature_degC = lps22hhTemperature_degC;

	/*
	The ALTITUDE value calculated is actually "Pressure Altitude". This lacks correction for temperature (and humidity)
	"pressure altitude" calculator located at: https://www.weather.gov/epz/wxcalc_pressurealtitude
	"pressure altitude" formula is defined at: https://www.weather.gov/media/epz/wxcalc/pressureAltitude.pdf
	 altitude in feet = 145366.45 * (1 - (hPa / 1013.25) ^ 0.190284) feet
	 altitude in meters = 145366.45 * 0.3048 * (1 - (hPa / 1013.25) ^ 0.190284) meters
	*/
	// weather.com formula
	//altitude = 44307.69396 * (1 - powf((atm / 1013.25), 0.190284));  // pressure altitude in meters
	// Bosch's formula
	altitude = 44330 * (1 - powf((pressure_hPa / 1013.25), 1 / 5.255));  // pressure altitude in meters

	Log_Debug("ALSPT19: Ambient Light[Lux] : %.2f\r\n", light_sensor);

	//// OLED
	update_oled();

#if (defined(IOT_CENTRAL_APPLICATION) || defined(IOT_HUB_APPLICATION))

	// We've seen that the first read of the Accelerometer data is garbage.  If this is the first pass
	// reading data, don't report it to Azure.  Since we're graphing data in Azure, this data point
	// will skew the data.
	if (!firstPass) {

		// Allocate memory for a telemetry message to Azure
		char *pjsonBuffer = (char *)malloc(JSON_BUFFER_SIZE);
		if (pjsonBuffer == NULL) {
			Log_Debug("ERROR: not enough memory to send telemetry");
		}

		snprintf(pjsonBuffer, JSON_BUFFER_SIZE, "{\"gX\":\"%.2lf\", \"gY\":\"%.2lf\", \"gZ\":\"%.2lf\", \"aX\": \"%.2f\", \"aY\": \"%.2f\", \"aZ\": \"%.2f\", \"pressure\": \"%.2f\", \"light_intensity\": \"%.2f\", \"altitude\": \"%.2f\", \"temp\": \"%.2f\",  \"rssi\": \"%d\"}",
			angular_rate_dps[0], angular_rate_dps[1], angular_rate_dps[2], acceleration_mg[0], acceleration_mg[1], acceleration_mg[2], pressure_hPa, light_sensor, altitude, lsm6dsoTemperature_degC, network_data.rssi);

		Log_Debug("\n[Info] Sending telemetry: %s\n", pjsonBuffer);
		AzureIoT_SendMessage(pjsonBuffer);
		free(pjsonBuffer);

}

	firstPass = false;

#endif

}

/// <summary>
///     Initializes the I2C interface.
/// </summary>
/// <returns>0 on success, or -1 on failure</returns>
int initI2c(void) {

	// Begin MT3620 I2C init

	i2cFd = I2CMaster_Open(MT3620_RDB_HEADER4_ISU2_I2C);
	if (i2cFd < 0) {
		Log_Debug("ERROR: I2CMaster_Open: errno=%d (%s)\n", errno, strerror(errno));
		return -1;
	}

	int result = I2CMaster_SetBusSpeed(i2cFd, I2C_BUS_SPEED_STANDARD);
	if (result != 0) {
		Log_Debug("ERROR: I2CMaster_SetBusSpeed: errno=%d (%s)\n", errno, strerror(errno));
		return -1;
	}

	result = I2CMaster_SetTimeout(i2cFd, 100);
	if (result != 0) {
		Log_Debug("ERROR: I2CMaster_SetTimeout: errno=%d (%s)\n", errno, strerror(errno));
		return -1;
	}

	// Start OLED
	if (oled_init())
	{
		Log_Debug("OLED not found!\n");
	}
	else
	{
		Log_Debug("OLED found!\n");
	}

	// Draw AVNET logo
	//oled_draw_logo();
	oled_i2c_bus_status(0);

	// Start lsm6dso specific init

	// Initialize lsm6dso mems driver interface
	dev_ctx.write_reg = platform_write;
	dev_ctx.read_reg = platform_read;
	dev_ctx.handle = &i2cFd;

	// Check device ID
	lsm6dso_device_id_get(&dev_ctx, &whoamI);
	if (whoamI != LSM6DSO_ID) {
		Log_Debug("LSM6DSO not found!\n");

		// OLED update
		lsm6dso_status = 1;
		oled_i2c_bus_status(1);
		return -1;
	}
	else {
		Log_Debug("LSM6DSO Found!\n");

		// OLED update
		lsm6dso_status = 0;
		oled_i2c_bus_status(1);
	}

	 // Restore default configuration
	lsm6dso_reset_set(&dev_ctx, PROPERTY_ENABLE);
	do {
		lsm6dso_reset_get(&dev_ctx, &rst);
	} while (rst);

	 // Disable I3C interface
	lsm6dso_i3c_disable_set(&dev_ctx, LSM6DSO_I3C_DISABLE);

	// Enable Block Data Update
	lsm6dso_block_data_update_set(&dev_ctx, PROPERTY_ENABLE);

	 // Set Output Data Rate
	lsm6dso_xl_data_rate_set(&dev_ctx, LSM6DSO_XL_ODR_12Hz5);
	lsm6dso_gy_data_rate_set(&dev_ctx, LSM6DSO_GY_ODR_12Hz5);

	 // Set full scale
	lsm6dso_xl_full_scale_set(&dev_ctx, LSM6DSO_4g);
	lsm6dso_gy_full_scale_set(&dev_ctx, LSM6DSO_2000dps);

	 // Configure filtering chain(No aux interface)
	// Accelerometer - LPF1 + LPF2 path
	lsm6dso_xl_hp_path_on_out_set(&dev_ctx, LSM6DSO_LP_ODR_DIV_100);
	lsm6dso_xl_filter_lp2_set(&dev_ctx, PROPERTY_ENABLE);

	// lps22hh specific init

	// Initialize lps22hh mems driver interface
	pressure_ctx.read_reg = lsm6dso_read_lps22hh_cx;
	pressure_ctx.write_reg = lsm6dso_write_lps22hh_cx;
	pressure_ctx.handle = &i2cFd;

	bool lps22hhDetected = false;
	int failCount = 10;

	while (!lps22hhDetected) {

		// Enable pull up on master I2C interface.
		lsm6dso_sh_pin_mode_set(&dev_ctx, LSM6DSO_INTERNAL_PULL_UP);

		// Check if LPS22HH is connected to Sensor Hub
		lps22hh_device_id_get(&pressure_ctx, &whoamI);
		if (whoamI != LPS22HH_ID) {
			Log_Debug("LPS22HH not found!\n");

			// OLED update
			lps22hh_status = 1;
			oled_i2c_bus_status(2);

		}
		else {
			lps22hhDetected = true;
			Log_Debug("LPS22HH Found!\n");

			// OLED update
			lps22hh_status = 0;
			oled_i2c_bus_status(2);
		}

		// Restore the default configuration
		lps22hh_reset_set(&pressure_ctx, PROPERTY_ENABLE);
		do {
			lps22hh_reset_get(&pressure_ctx, &rst);
		} while (rst);

		// Enable Block Data Update
		lps22hh_block_data_update_set(&pressure_ctx, PROPERTY_ENABLE);

		//Set Output Data Rate
		lps22hh_data_rate_set(&pressure_ctx, LPS22HH_10_Hz_LOW_NOISE);

		// If we failed to detect the lps22hh device, then pause before trying again.
		if (!lps22hhDetected) {
			HAL_Delay(100);
		}

		if (failCount-- == 0) {
			Log_Debug("Failed to read LSM22HH device ID, exiting\n");
			return -1;
		}


		// MCP23x17 specific init
		// Initialize MCP23X17 interface
		mcp23x17_ctx.read_reg = mcp23x17_read_cx;
		mcp23x17_ctx.write_reg = mcp23x17_write_cx;
		mcp23x17_ctx.handle = &i2cFd;

		bool mcp23x17Detected = false;
		int failCount = 10;

		while (!mcp23x17Detected) {
			// Check if mcp23x17Detected is connected
			mcp23x17_device_id_get(&mcp23x17_ctx, &whoamI);
			if (whoamI != MCP23X17_DEFAULT_HIGH) {
				Log_Debug("MCP23x17 not found!\n");

				// OLED update
				mcp23x17_status = 1;
				oled_i2c_bus_status(3);

			}
			else {
				mcp23x17Detected = true;
				Log_Debug("MCP23X17 Found!\n");

				// OLED update
				mcp23x17_status = 0;
				oled_i2c_bus_status(3);
			}

			// Initiallize the PortA for output and the PortB for Input(default)
			uint8_t setOuputBank = 0x00U;
			mcp23x17_write_reg(&mcp23x17_ctx, MCP23017_IODIRB, &setOuputBank, 1);

			uint8_t testRead = 0xffU;

			uint8_t test = mcp23x17_read_reg(&mcp23x17_ctx, MCP23017_IODIRB, &testRead, 1);

			if (testRead != 0x00) {
				Log_Debug("Failed to setup PortA for output");
			}

			// If we failed to detect the mcp23x17Detected device, then pause before trying again.
			if (!mcp23x17Detected) {
				HAL_Delay(100);
			}

			if (failCount-- == 0) {
				Log_Debug("Failed to read LSM22HH device ID, exiting\n");
				return -1;
			}

			// testing an led to light up
			uint8_t testOutput = 0x55U;

			ssize_t writeRet = mcp23x17_write_reg(&mcp23x17_ctx, MCP23017_GPIOB, &testOutput, 1);

			uint8_t readRet = mcp23x17_read_reg(&mcp23x17_ctx, MCP23017_GPIOB, &testRead, 1);
		}
	}

	// Read the raw angular rate data from the device to use as offsets.  We're making the assumption that the device
	// is stationary.

	uint8_t reg;


	Log_Debug("LSM6DSO: Calibrating angular rate . . .\n");
	Log_Debug("LSM6DSO: Please make sure the device is stationary.\n");

	do {
		// Read the calibration values
		lsm6dso_gy_flag_data_ready_get(&dev_ctx, &reg);
		if (reg)
		{
			// Read angular rate field data to use for calibration offsets
			memset(data_raw_angular_rate.u8bit, 0x00, 3 * sizeof(int16_t));
			lsm6dso_angular_rate_raw_get(&dev_ctx, raw_angular_rate_calibration.u8bit);
		}

		// Read the angular data rate again and verify that after applying the calibration, we have 0 angular rate in all directions

		lsm6dso_gy_flag_data_ready_get(&dev_ctx, &reg);
		if (reg)
		{
			// Read angular rate field data
			memset(data_raw_angular_rate.u8bit, 0x00, 3 * sizeof(int16_t));
			lsm6dso_angular_rate_raw_get(&dev_ctx, data_raw_angular_rate.u8bit);

			// Before we store the mdps values subtract the calibration data we captured at startup.
			angular_rate_dps[0] = lsm6dso_from_fs2000_to_mdps(data_raw_angular_rate.i16bit[0] - raw_angular_rate_calibration.i16bit[0]);
			angular_rate_dps[1] = lsm6dso_from_fs2000_to_mdps(data_raw_angular_rate.i16bit[1] - raw_angular_rate_calibration.i16bit[1]);
			angular_rate_dps[2] = lsm6dso_from_fs2000_to_mdps(data_raw_angular_rate.i16bit[2] - raw_angular_rate_calibration.i16bit[2]);
		}

	// If the angular values after applying the offset are not zero, then do it again!
	} while (angular_rate_dps[0] == angular_rate_dps[1] == angular_rate_dps[2] == 0.0);

	Log_Debug("LSM6DSO: Calibrating angular rate complete!\n");


	// Init the epoll interface to periodically run the AccelTimerEventHandler routine where we read the sensors

	// Define the period in the build_options.h file
	struct timespec accelReadPeriod = { .tv_sec = ACCEL_READ_PERIOD_SECONDS,.tv_nsec = ACCEL_READ_PERIOD_NANO_SECONDS };
	// event handler data structures. Only the event handler field needs to be populated.
	static EventData accelEventData = { .eventHandler = &AccelTimerEventHandler };
	accelTimerFd = CreateTimerFdAndAddToEpoll(epollFd, &accelReadPeriod, &accelEventData, EPOLLIN);
	if (accelTimerFd < 0) {
		return -1;
	}

	return 0;
}

/// <summary>
///     Closes the I2C interface File Descriptors.
/// </summary>
void closeI2c(void) {

	CloseFdAndPrintError(i2cFd, "i2c");
	CloseFdAndPrintError(accelTimerFd, "accelTimer");
}

/// <summary>
///     Writes data to the lsm6dso i2c device
/// </summary>
/// <returns>0</returns>

static int32_t platform_write(int *fD, uint8_t reg, uint8_t *bufp,
	uint16_t len)
{

#ifdef ENABLE_READ_WRITE_DEBUG
	Log_Debug("platform_write()\n");
	Log_Debug("reg: %0x\n", reg);
	Log_Debug("len: %0x\n", len);
	Log_Debug("bufp contents: ");
	for (int i = 0; i < len; i++) {

		Log_Debug("%0x: ", bufp[i]);
	}
	Log_Debug("\n");
#endif

	// Construct a new command buffer that contains the register to write to, then the data to write
	uint8_t cmdBuffer[len + 1];
	cmdBuffer[0] = reg;
	for (int i = 0; i < len; i++) {
		cmdBuffer[i + 1] = bufp[i];
	}

#ifdef ENABLE_READ_WRITE_DEBUG
	Log_Debug("cmdBuffer contents: ");
	for (int i = 0; i < len + 1; i++) {

		Log_Debug("%0x: ", cmdBuffer[i]);
	}
	Log_Debug("\n");
#endif

	// Write the data to the device
	int32_t retVal = I2CMaster_Write(*fD, lsm6dsOAddress, cmdBuffer, (size_t)len + 1);
	if (retVal < 0) {
		Log_Debug("ERROR: platform_write: errno=%d (%s)\n", errno, strerror(errno));
		return -1;
	}
#ifdef ENABLE_READ_WRITE_DEBUG
	Log_Debug("Wrote %d bytes to device.\n\n", retVal);
#endif
	return 0;
}

/// <summary>
///     Reads generic device register from the i2c interface
/// </summary>
/// <returns>0</returns>

/*
 * @brief  Read generic device register (platform dependent)
 *
 * @param  handle    customizable argument. In this examples is used in
 *                   order to select the correct sensor bus handler.
 * @param  reg       register to read
 * @param  bufp      pointer to buffer that store the data read
 * @param  len       number of consecutive register to read
 *
 */
static int32_t platform_read(int *fD, uint8_t reg, uint8_t *bufp,
	uint16_t len)
{

#ifdef ENABLE_READ_WRITE_DEBUG
	Log_Debug("platform_read()\n");
	Log_Debug("reg: %0x\n", reg);
	Log_Debug("len: %d\n", len);
;
#endif

	// Set the register address to read
	int32_t retVal = I2CMaster_Write(i2cFd, lsm6dsOAddress, &reg, 1);
	if (retVal < 0) {
		Log_Debug("ERROR: platform_read(write step): errno=%d (%s)\n", errno, strerror(errno));
		return -1;
	}

	// Read the data into the provided buffer
	retVal = I2CMaster_Read(i2cFd, lsm6dsOAddress, bufp, len);
	if (retVal < 0) {
		Log_Debug("ERROR: platform_read(read step): errno=%d (%s)\n", errno, strerror(errno));
		return -1;
	}

#ifdef ENABLE_READ_WRITE_DEBUG
	Log_Debug("Read returned: ");
	for (int i = 0; i < len; i++) {
		Log_Debug("%0x: ", bufp[i]);
	}
	Log_Debug("\n\n");
#endif

	return 0;
}
/*
 * @brief  Write lsm2mdl device register (used by configuration functions)
 *
 * @param  handle    customizable argument. In this examples is used in
 *                   order to select the correct sensor bus handler.
 * @param  reg       register to write
 * @param  bufp      pointer to data to write in register reg
 * @param  len       number of consecutive register to write
 *
 */
static int32_t lsm6dso_write_lps22hh_cx(void* ctx, uint8_t reg, uint8_t* data,
	uint16_t len)
{
	axis3bit16_t data_raw_acceleration;
	int32_t ret;
	uint8_t drdy;
	lsm6dso_status_master_t master_status;
	lsm6dso_sh_cfg_write_t sh_cfg_write;

	// Configure Sensor Hub to write to the LPS22HH, and send the write data
	sh_cfg_write.slv0_add = (LPS22HH_I2C_ADD_L & 0xFEU) >> 1; // 7bit I2C address
	sh_cfg_write.slv0_subadd = reg,
	sh_cfg_write.slv0_data = *data,
	ret = lsm6dso_sh_cfg_write(&dev_ctx, &sh_cfg_write);

	/* Disable accelerometer. */
	lsm6dso_xl_data_rate_set(&dev_ctx, LSM6DSO_XL_ODR_OFF);

	/* Enable I2C Master. */
	lsm6dso_sh_master_set(&dev_ctx, PROPERTY_ENABLE);

	/* Enable accelerometer to trigger Sensor Hub operation. */
	lsm6dso_xl_data_rate_set(&dev_ctx, LSM6DSO_XL_ODR_104Hz);

	/* Wait Sensor Hub operation flag set. */
	lsm6dso_acceleration_raw_get(&dev_ctx, data_raw_acceleration.u8bit);
	do
	{
		HAL_Delay(20);
		lsm6dso_xl_flag_data_ready_get(&dev_ctx, &drdy);
	} while (!drdy);

	do
	{
		HAL_Delay(20);
		lsm6dso_sh_status_get(&dev_ctx, &master_status);
	} while (!master_status.sens_hub_endop);

	/* Disable I2C master and XL (trigger). */
	lsm6dso_sh_master_set(&dev_ctx, PROPERTY_DISABLE);
	lsm6dso_xl_data_rate_set(&dev_ctx, LSM6DSO_XL_ODR_OFF);

	return ret;
}

/*
 * @brief  Read lsm2mdl device register (used by configuration functions)
 *
 * @param  handle    customizable argument. In this examples is used in
 *                   order to select the correct sensor bus handler.
 * @param  reg       register to read
 * @param  bufp      pointer to buffer that store the data read
 * @param  len       number of consecutive register to read
 *
 */
static int32_t lsm6dso_read_lps22hh_cx(void* ctx, uint8_t reg, uint8_t* data, uint16_t len)
{
	lsm6dso_sh_cfg_read_t sh_cfg_read;
	axis3bit16_t data_raw_acceleration;
	int32_t ret;
	uint8_t drdy;
	lsm6dso_status_master_t master_status;

	/* Disable accelerometer. */
	lsm6dso_xl_data_rate_set(&dev_ctx, LSM6DSO_XL_ODR_OFF);

	// For each byte we need to read from the lps22hh
	for (int i = 0; i < len; i++) {

		/* Configure Sensor Hub to read LPS22HH. */
		sh_cfg_read.slv_add = (LPS22HH_I2C_ADD_L &0xFEU) >> 1; /* 7bit I2C address */
		sh_cfg_read.slv_subadd = reg+i;
		sh_cfg_read.slv_len = 1;

		// Call the command to read the data from the sensor hub.
		// This data will be read from the device connected to the
		// sensor hub, and saved into a register for us to read.
		ret = lsm6dso_sh_slv0_cfg_read(&dev_ctx, &sh_cfg_read);
		lsm6dso_sh_slave_connected_set(&dev_ctx, LSM6DSO_SLV_0);

		/* Enable I2C Master and I2C master. */
		lsm6dso_sh_master_set(&dev_ctx, PROPERTY_ENABLE);

		/* Enable accelerometer to trigger Sensor Hub operation. */
		lsm6dso_xl_data_rate_set(&dev_ctx, LSM6DSO_XL_ODR_104Hz);

		/* Wait Sensor Hub operation flag set. */
		lsm6dso_acceleration_raw_get(&dev_ctx, data_raw_acceleration.u8bit);
		do {
			HAL_Delay(20);
			lsm6dso_xl_flag_data_ready_get(&dev_ctx, &drdy);
		} while (!drdy);

		do {
			HAL_Delay(20);
			lsm6dso_sh_status_get(&dev_ctx, &master_status);
		} while (!master_status.sens_hub_endop);

		/* Disable I2C master and XL(trigger). */
		lsm6dso_sh_master_set(&dev_ctx, PROPERTY_DISABLE);
		lsm6dso_xl_data_rate_set(&dev_ctx, LSM6DSO_XL_ODR_OFF);

		// Read the data from the device.  The call below reads
		// all 18 sensor hub data.  We just need the data from
		// sensor hub 1, so copy that into our data array.
		uint8_t buffer[18];
		lsm6dso_sh_read_data_raw_get(&dev_ctx, buffer);
		data[i] = buffer[1];

#ifdef ENABLE_READ_WRITE_DEBUG
		Log_Debug("Read %d bytes: ", len);
		for (int i = 0; i < len; i++) {
			Log_Debug("[%0x] ", data[i]);
		}
		Log_Debug("\n", len);
#endif
	}

	/* Re-enable accelerometer */
	lsm6dso_xl_data_rate_set(&dev_ctx, LSM6DSO_XL_ODR_104Hz);

	return ret;
}

/*
 * @brief  Read lsm2mdl device register (used by configuration functions)
 *
 * @param  handle    customizable argument. In this examples is used in
 *                   order to select the correct sensor bus handler.
 * @param  reg       register to read
 * @param  bufp      pointer to buffer that store the data read
 * @param  len       number of consecutive register to read
 *
 */
static uint8_t mcp23x17_read_cx(mcp23x17_ctx_t* ctx, uint8_t reg, uint8_t* data, uint8_t len)
{
	ssize_t ret;
	int test = *((int*)ctx->handle);
	const uint8_t command[] = { reg, data };

	// Send the data by I2C bus
	// tried todo this the applibs way instead of the posix way.  I am sure I missed a memo....
	int targetSet = I2CMaster_SetDefaultTargetAddress(*((int*)ctx->handle), mcp23x17_DEFAULT_ADDR);
	int targetRegisterWrite = write(*((int*)ctx->handle), &reg, len);
	ssize_t readRet = read(*((int*)ctx->handle), data, len);
	ret = readRet;

#ifdef ENABLE_READ_WRITE_DEBUG
		Log_Debug("Read %d bytes: ", len);
		for (int i = 0; i < len; i++) {
			Log_Debug("[%0x] ", data[i]);
		}
		Log_Debug("\n", len);
#endif

	return ret;
}

/*
 * @brief  Write mcp23x17 device register
 *
 * @param  handle    customizable argument. In this examples is used in
 *                   order to select the correct sensor bus handler.
 * @param  reg       register to write
 * @param  bufp      pointer to data to write in register reg
 * @param  len       number of consecutive register to write
 *
 */
static uint8_t mcp23x17_write_cx(mcp23x17_ctx_t* ctx, uint8_t reg, uint8_t* data, uint8_t len)
{
	ssize_t ret;
	const uint8_t command[] = { reg, *data };

	ret = I2CMaster_Write(*((int*)ctx->handle), mcp23x17_DEFAULT_ADDR, command, sizeof(command));

	return ret;
}
