pulcher/secureMoodTracker/secure-mt/secure-mt/oled.c

/***************************************************************************************************
   Name: OLED.c
   Sphere OS: 19.05
****************************************************************************************************/

#include "oled.h"
#include <math.h>

uint8_t oled_state = 0;

// Data of sensors (Acceleration, Gyro, Temperature, Presure)
sensor_var sensor_data;

// Data of network status
network_var network_data;

// Data of light sensor
float light_sensor;

// Altitude
extern float altitude;

// Array with messages from Azure
//extern uint8_t oled_ms1[CLOUD_MSG_SIZE];
//extern uint8_t oled_ms2[CLOUD_MSG_SIZE];
//extern uint8_t oled_ms3[CLOUD_MSG_SIZE];
//extern uint8_t oled_ms4[CLOUD_MSG_SIZE];

// Status variables of I2C bus and RT core
extern uint8_t RTCore_status;
extern uint8_t lsm6dso_status;
extern uint8_t lps22hh_status;
extern uint8_t mcp23x17_status;

/**
  * @brief  OLED initialization.
  * @param  None.
  * @retval Positive if was unsuccefully, zero if was succefully.
  */
uint8_t oled_init()
{
	return sd1306_init();
}

// State machine to change the OLED status
void update_oled()
{
	switch (oled_state)
	{
		//case 0:
		//{
		//	oled_i2c_bus_status(4);
		//}
		//break;
		//case 1:
		//{
		//	update_network();
		//}
		//break;
		//case 2:
		//{
		//	clear_oled_buffer();
		//	sd1306_draw_string(0, 0, " Cloud Twin", FONT_SIZE_TITLE, white_pixel);

		//	//sd1306_draw_string(OLED_LINE_1_X, OLED_LINE_1_Y, oled_ms1, FONT_SIZE_LINE, white_pixel);
		//	//sd1306_draw_string(OLED_LINE_2_X, OLED_LINE_2_Y, oled_ms2, FONT_SIZE_LINE, white_pixel);
		//	//sd1306_draw_string(OLED_LINE_3_X, OLED_LINE_3_Y, oled_ms3, FONT_SIZE_LINE, white_pixel);
		//	//sd1306_draw_string(OLED_LINE_4_X, OLED_LINE_4_Y, oled_ms4, FONT_SIZE_LINE, white_pixel);

		//	sd1306_refresh();
		//}
		//break;
		//case 3:
		//{
		//	update_accel(sensor_data.acceleration_mg[0], sensor_data.acceleration_mg[1], sensor_data.acceleration_mg[2]);
		//}
		//break;
		//case 4:
		//{
		//	update_angular_rate(sensor_data.angular_rate_dps[0], sensor_data.angular_rate_dps[1], sensor_data.angular_rate_dps[2]);
		//}
		//break;
		//case 5:
		//{
		//	update_environ(sensor_data.lsm6dsoTemperature_degC, sensor_data.lps22hhTemperature_degC, sensor_data.lps22hhpressure_hPa);
		//}
		//break;
		//case 6:
		//{
		//	update_other(light_sensor, 0, 0);
		//}
		//break;
		//case 7:
		//{
		//	oled_draw_logo();
		//}
		//break;

		default:
		break;
	}
}

/**
  * @brief  Template to show I2C bus status
  * @param  sensor_number: Sensor number
  * @param  sensor_status: Sensor status
  * @retval None.
  */
void oled_i2c_bus_status(uint8_t sensor_number, float currentMood, int voteCount, int motionCount)
{
	char buf[48] = {0};

	// Strings for labels
	uint8_t titleMessage[] = "Mood-A-Tron";
	//uint8_t str_bus_sta[]   = "I2C Bus Status:";
	//uint8_t str_lsmod_sta[] = "LSM6DSO Accel.:";
	//uint8_t str_lps22_sta[] = "LPS22HH Barom.:";
	uint8_t str_mcp23x17_sta[] = "MCP23X17 GPIO.:";
	//uint8_t str_rtcore_sta[] = "Real Time Core:";
	uint8_t avgMoodMessage[] = "Average mood:";
	uint8_t totalVoteMessage[] = "Total votes:";
	uint8_t motionSeen[] = "Motion count:";

	switch (sensor_number)
	{
		case 0:
		{
			// Clear OLED buffer
			clear_oled_buffer();

			// Draw the title
			//sd1306_draw_string(OLED_TITLE_X, OLED_TITLE_Y, " I2C Init", FONT_SIZE_TITLE, white_pixel);
			sd1306_draw_string(OLED_TITLE_X, OLED_TITLE_Y, titleMessage, FONT_SIZE_TITLE, white_pixel);

			// Draw the current mood average label
			sd1306_draw_string(OLED_LINE_2_X, OLED_LINE_2_Y, avgMoodMessage, FONT_SIZE_LINE, white_pixel);
			snprintf(buf, sizeof(buf), "%f", currentMood);
			sd1306_draw_string(sizeof(avgMoodMessage) * 6, OLED_LINE_2_Y, buf, FONT_SIZE_LINE, white_pixel);

			// Draw the total number of votes label
			sd1306_draw_string(OLED_LINE_3_X, OLED_LINE_3_Y, totalVoteMessage, FONT_SIZE_LINE, white_pixel);
			snprintf(buf, sizeof(buf), "%d", voteCount);
			sd1306_draw_string(sizeof(totalVoteMessage) * 6, OLED_LINE_3_Y, buf, FONT_SIZE_LINE, white_pixel);

			// Draw the amount of movement detected label
			sd1306_draw_string(OLED_LINE_5_X, OLED_LINE_5_Y, motionSeen, FONT_SIZE_LINE, white_pixel);
			if (motionCount >= 0) {
				snprintf(buf, sizeof(buf), "%d", motionCount);
			}
			else {
				snprintf(buf, sizeof(buf), "disabled");
			}
			sd1306_draw_string(sizeof(motionSeen) * 6, OLED_LINE_5_Y, buf, FONT_SIZE_LINE, white_pixel);

			// Draw a label at line 1
			//sd1306_draw_string(OLED_LINE_1_X, OLED_LINE_1_Y, str_bus_sta, FONT_SIZE_LINE, white_pixel);

			//// I2C bus OK, if not OLED doesn't show a image
			//sd1306_draw_string(sizeof(str_bus_sta) * 6, OLED_LINE_1_Y, "OK", FONT_SIZE_LINE, white_pixel);
		}
		break;
		case 1:
		{
			// Draw a label at line 2
			//sd1306_draw_string(OLED_LINE_2_X, OLED_LINE_2_Y, str_lsmod_sta, FONT_SIZE_LINE, white_pixel);

			// Show LSMOD status
			//if (lsm6dso_status == 0)
			//{
			//	sd1306_draw_string(sizeof(str_lsmod_sta) * 6, OLED_LINE_2_Y, "OK", FONT_SIZE_LINE, white_pixel);
			//}
			//else
			//{
			//	sd1306_draw_string(sizeof(str_lsmod_sta) * 6, OLED_LINE_2_Y, "ERROR", FONT_SIZE_LINE, white_pixel);
			//}
		}
		break;
		case 2:
		{
			// Draw a label at line 3
			//sd1306_draw_string(OLED_LINE_3_X, OLED_LINE_3_Y, str_lps22_sta, FONT_SIZE_LINE, white_pixel);

			//// Show LPS22 status
			//if (lps22hh_status == 0)
			//{
			//	sd1306_draw_string(sizeof(str_lps22_sta) * 6, OLED_LINE_3_Y, "OK", FONT_SIZE_LINE, white_pixel);
			//}
			//else
			//{
			//	sd1306_draw_string(sizeof(str_lps22_sta) * 6, OLED_LINE_3_Y, "ERROR", FONT_SIZE_LINE, white_pixel);
			//}
		}
		break;
		case 3:
		{
			// Draw a label at line 3
			//sd1306_draw_string(OLED_LINE_4_X, OLED_LINE_4_Y, str_mcp23x17_sta, FONT_SIZE_LINE, white_pixel);

			// Show mcp23017 status
			if (mcp23x17_status == 0)
			{
				sd1306_draw_string(sizeof(str_mcp23x17_sta) * 6, OLED_LINE_4_Y, "OK", FONT_SIZE_LINE, white_pixel);
			}
			else
			{
				sd1306_draw_string(sizeof(str_mcp23x17_sta) * 6, OLED_LINE_4_Y, "ERROR", FONT_SIZE_LINE, white_pixel);
			}
		}
		break;
		case 4:
		{
			// If we are here I2C is working well

			// Clear OLED buffer
			clear_oled_buffer();

			// Draw the title
			//sd1306_draw_string(OLED_TITLE_X, OLED_TITLE_Y, " I2C Init", FONT_SIZE_TITLE, white_pixel);

			//// Draw a label at line 1
			//sd1306_draw_string(OLED_LINE_1_X, OLED_LINE_1_Y, str_bus_sta, FONT_SIZE_LINE, white_pixel);

			//// I2C bus OK, if not OLED doesn't show a image
			//sd1306_draw_string(sizeof(str_bus_sta) * 6, OLED_LINE_1_Y, "OK", FONT_SIZE_LINE, white_pixel);

			//// Draw a label at line 2
			//sd1306_draw_string(OLED_LINE_2_X, OLED_LINE_2_Y, str_lsmod_sta, FONT_SIZE_LINE, white_pixel);

			// Show LSMOD status
			//if (lsm6dso_status == 0)
			//{
			//	sd1306_draw_string(sizeof(str_lsmod_sta) * 6, OLED_LINE_2_Y, "OK", FONT_SIZE_LINE, white_pixel);
			//}
			//else
			//{
			//	sd1306_draw_string(sizeof(str_lsmod_sta) * 6, OLED_LINE_2_Y, "ERROR", FONT_SIZE_LINE, white_pixel);
			//}

			// Draw a label at line 3
			// sd1306_draw_string(OLED_LINE_3_X, OLED_LINE_3_Y, str_lps22_sta, FONT_SIZE_LINE, white_pixel);

			//// Show LPS22 status
			//if (lps22hh_status == 0)
			//{
			//	sd1306_draw_string(sizeof(str_lps22_sta) * 6, OLED_LINE_3_Y, "OK", FONT_SIZE_LINE, white_pixel);
			//}
			//else
			//{
			//	sd1306_draw_string(sizeof(str_lps22_sta) * 6, OLED_LINE_3_Y, "ERROR", FONT_SIZE_LINE, white_pixel);
			//}

			// Draw a label at line 5
			// sd1306_draw_string(OLED_LINE_5_X, OLED_LINE_5_Y, str_rtcore_sta, FONT_SIZE_LINE, white_pixel);

			// Show RTcore status
			//if ( RTCore_status == 0)
			//{
			//	sd1306_draw_string(sizeof(str_rtcore_sta) * 6, OLED_LINE_5_Y, "OK", FONT_SIZE_LINE, white_pixel);
			//}
			//else
			//{
			//	sd1306_draw_string(sizeof(str_rtcore_sta) * 6, OLED_LINE_5_Y, "ERROR", FONT_SIZE_LINE, white_pixel);
			//}
		}
		break;
		default:
		break;
	}

	// Send the buffer to OLED RAM
	sd1306_refresh();
}

/**
  * @brief  Get the channel at given frequency
  * @param  freq_MHz: Frequency in MHz
  * @retval Channel.
  */
uint16_t get_channel(uint16_t freq_MHz)
{
	if (freq_MHz < 5000 && freq_MHz > 2400)
	{
		// channel of in 2.4 GHz band
		freq_MHz -= 2407;
	}
	else if(freq_MHz > 5000)
	{
		// channel of in 5 GHz band
		freq_MHz -= 5000;
	}
	else
	{
		// channel not in 2.4 or 5 GHz bands
		freq_MHz = 0;
	}

	freq_MHz /= 5;

	return freq_MHz;
}

/**
  * @brief  Template to show Network status
  * @param  None
  * @retval None.
  */
void update_network()
{
	uint8_t string_data[10];
	uint16_t channel;
	uint8_t aux_size;

	// Strings for labels
	uint8_t str_SSID[] = "SSID:";
	uint8_t str_freq[] = "Freq:";
	uint8_t str_RSSI[] = "RSSI:";
	uint8_t str_chan[] = "Chan:";

	uint8_t aux_data_str[] = "%d";

	// Clear oled buffer
	clear_oled_buffer();

	// Draw the title
	sd1306_draw_string(OLED_TITLE_X, OLED_TITLE_Y, "  Network", FONT_SIZE_TITLE, white_pixel);

	// Draw a label at line 1
	sd1306_draw_string(OLED_LINE_1_X, OLED_LINE_1_Y, str_SSID, FONT_SIZE_LINE, white_pixel);
	// Draw SSID string
	sd1306_draw_string(sizeof(str_SSID)*6, OLED_LINE_1_Y, network_data.SSID, FONT_SIZE_LINE, white_pixel);


	// Draw a label at line 2
	sd1306_draw_string(OLED_LINE_2_X, OLED_LINE_2_Y, str_freq, FONT_SIZE_LINE, white_pixel);

	// Convert frequency value to string
	intToStr(network_data.frequency_MHz, string_data, 1);

	// Draw frequency value
	sd1306_draw_string(sizeof(str_freq) * 6, OLED_LINE_2_Y, string_data, FONT_SIZE_LINE, white_pixel);
	// Draw the units
	//sd1306_draw_string(sizeof(str_freq) * 6 + (get_str_size(string_data)+1) * 6, OLED_LINE_2_Y, "MHz", FONT_SIZE_LINE, white_pixel);


	// Draw channel label at line 2
	sd1306_draw_string(sizeof(str_freq) * 6 + (get_str_size(string_data) + 1) * 6, OLED_LINE_2_Y, str_chan, FONT_SIZE_LINE, white_pixel);

	channel = get_channel(network_data.frequency_MHz);

	aux_size = get_str_size(string_data);

	// Convert frequency value to string
	intToStr(channel, string_data, 1);

	// Draw channel value
	sd1306_draw_string(sizeof(str_freq) * 6 + (aux_size + sizeof(str_chan)+ 1) * 6, OLED_LINE_2_Y, string_data, FONT_SIZE_LINE, white_pixel);

	// Draw a label at line 3
	sd1306_draw_string(OLED_LINE_3_X, OLED_LINE_3_Y, str_RSSI, FONT_SIZE_LINE, white_pixel);

	// Convert RSSI value to string (Currently RSSI is always zero)
	intToStr(network_data.rssi, string_data, 1);

	strcpy(string_data, "%d");
	snprintf(string_data, 10, aux_data_str, network_data.rssi);

	// Draw RSSI value
	sd1306_draw_string(sizeof(str_RSSI) * 6, OLED_LINE_3_Y, string_data, FONT_SIZE_LINE, white_pixel);

	// Draw dBm unit
	sd1306_draw_string(sizeof(str_freq) * 6 + (get_str_size(string_data) + 1) * 6, OLED_LINE_3_Y, "dBm", FONT_SIZE_LINE, white_pixel);

	// Send the buffer to OLED RAM
	sd1306_refresh();
}

/**
  * @brief  Template to show Acceleration data
  * @param  x: Acceleration in axis X
  * @param  y: Acceleration in axis Y
  * @param  z: Acceleration in axis Z
  * @retval None.
  */
void update_accel(float x, float y, float z)
{
	uint32_t i;
	uint8_t string_data[10];

	// Strings for labels
	uint8_t str_ax[] = "Axis X:";
	uint8_t str_ay[] = "Axis Y:";
	uint8_t str_az[] = "Axis Z:";

	// Clear OLED buffer
	clear_oled_buffer();

	// Draw the title
	sd1306_draw_string(OLED_TITLE_X, OLED_TITLE_Y, "   Accel.", FONT_SIZE_TITLE, white_pixel);

	// Convert x value to string
	ftoa(x, string_data, 2);

	// Draw a label at line 1
	sd1306_draw_string(OLED_LINE_1_X, OLED_LINE_1_Y, str_ax, FONT_SIZE_LINE, white_pixel);
	// Draw the value of x
	sd1306_draw_string(sizeof(str_ax) * 6, OLED_LINE_1_Y, string_data, FONT_SIZE_LINE, white_pixel);
	// Draw the units of x
	sd1306_draw_string(sizeof(str_ax) * 6 + (get_str_size(string_data) + 1) * 6, OLED_LINE_1_Y, "mg", FONT_SIZE_LINE, white_pixel);

	// Convert y value to string
	ftoa(y, string_data, 2);

	// Draw a label at line 2
	sd1306_draw_string(OLED_LINE_2_X, OLED_LINE_2_Y, str_ay, FONT_SIZE_LINE, white_pixel);
	// Draw the value of y
	sd1306_draw_string(sizeof(str_az) * 6, OLED_LINE_2_Y, string_data, FONT_SIZE_LINE, white_pixel);
	// Draw the units of y
	sd1306_draw_string(sizeof(str_ay) * 6 + (get_str_size(string_data) + 1) * 6, OLED_LINE_2_Y, "mg", FONT_SIZE_LINE, white_pixel);

	// Convert z value to string
	ftoa(z, string_data, 2);

	// Draw a label at line 3
	sd1306_draw_string(OLED_LINE_3_X, OLED_LINE_3_Y, str_az, FONT_SIZE_LINE, white_pixel);
	// Draw the value of z
	sd1306_draw_string(sizeof(str_az) * 6, OLED_LINE_3_Y, string_data, FONT_SIZE_LINE, white_pixel);
	// Draw the units of z
	sd1306_draw_string(sizeof(str_az) * 6 + (get_str_size(string_data) + 1) * 6, OLED_LINE_3_Y, "mg", FONT_SIZE_LINE, white_pixel);

	// Send the buffer to OLED RAM
	sd1306_refresh();
}

/**
  * @brief  Template to show Angular rate data
  * @param  x: Angular rate in axis X
  * @param  y: Angular rate in axis Y
  * @param  z: Angular rate in axis Z
  * @retval None.
  */
void update_angular_rate(float x, float y, float z)
{
	uint32_t i;
	uint8_t string_data[10];

	// Strings for labels
	uint8_t str_gx[] = "GX:";
	uint8_t str_gy[] = "GY:";
	uint8_t str_gz[] = "GZ:";

	// Clear OLED buffer
	clear_oled_buffer();

	// Draw the title
	sd1306_draw_string(OLED_TITLE_X, OLED_TITLE_Y, "   Gyro.", FONT_SIZE_TITLE, white_pixel);

	// Convert x value to string
	ftoa(x, string_data, 2);

	// Draw a label at line 1
	sd1306_draw_string(OLED_LINE_1_X, OLED_LINE_1_Y, str_gx, FONT_SIZE_LINE, white_pixel);
	// Draw the value of x
	sd1306_draw_string(sizeof(str_gx) * 6, OLED_LINE_1_Y, string_data, FONT_SIZE_LINE, white_pixel);
	// Draw the units of x
	sd1306_draw_string(sizeof(str_gx) * 6 + (get_str_size(string_data) + 1) * 6, OLED_LINE_1_Y, "dps", FONT_SIZE_LINE, white_pixel);

	// Convert y value to string
	ftoa(y, string_data, 2);

	// Draw a label at line 2
	sd1306_draw_string(OLED_LINE_2_X, OLED_LINE_2_Y, str_gy, FONT_SIZE_LINE, white_pixel);
	// Draw the value of y
	sd1306_draw_string(sizeof(str_gy) * 6, OLED_LINE_2_Y, string_data, FONT_SIZE_LINE, white_pixel);
	// Draw the units of y
	sd1306_draw_string(sizeof(str_gy) * 6 + (get_str_size(string_data) + 1) * 6, OLED_LINE_2_Y, "dps", FONT_SIZE_LINE, white_pixel);

	// Convert z value to string
	ftoa(z, string_data, 2);

	// Draw a label at line 3
	sd1306_draw_string(OLED_LINE_3_X, OLED_LINE_3_Y, str_gz, FONT_SIZE_LINE, white_pixel);
	// Draw the value of z
	sd1306_draw_string(sizeof(str_gz) * 6, OLED_LINE_3_Y, string_data, FONT_SIZE_LINE, white_pixel);
	// Draw the units of z
	sd1306_draw_string(sizeof(str_gz) * 6 + (get_str_size(string_data) + 1) * 6, OLED_LINE_3_Y, "dps", FONT_SIZE_LINE, white_pixel);

	// Send the buffer to OLED RAM
	sd1306_refresh();
}

/**
  * @brief  Template to show Enviromental data
  * @param  temp1: Temperature 1 in celsius degrees
  * @param  temp2: Temperature 2 in celsius degrees
  * @param  atm: Presure in hPa
  * @retval None.
  */
void update_environ(float temp1, float temp2, float atm)
{
	uint32_t i;
	uint8_t string_data[10];

	// Strings for labels
	uint8_t str_temp1[] = "Temp1:";
	uint8_t str_temp2[] = "Temp2:";
	uint8_t str_atm[] = "Barom:";
	uint8_t str_altitude[] = "Elev :";

	// Clear OLED buffer
	clear_oled_buffer();

	// Draw the title
	sd1306_draw_string(OLED_TITLE_X, OLED_TITLE_Y, "  Environ.", FONT_SIZE_TITLE, white_pixel);

	// Convert temp1 value to string
	ftoa(temp1, string_data, 2);

	// Draw a label at line 1
	sd1306_draw_string(OLED_LINE_1_X, OLED_LINE_1_Y, str_temp1, FONT_SIZE_LINE, white_pixel);
	// Draw the value of temp1
	sd1306_draw_string(sizeof(str_temp1) * 6, OLED_LINE_1_Y, string_data, FONT_SIZE_LINE, white_pixel);
	// Draw the units of temp1
	sd1306_draw_string(sizeof(str_temp1) * 6 + (get_str_size(string_data) + 1) * 6, OLED_LINE_1_Y, "°C", FONT_SIZE_LINE, white_pixel);

	// Convert temp2 value to string
	ftoa(temp2, string_data, 2);

	// Draw a label at line 2
	sd1306_draw_string(OLED_LINE_2_X, OLED_LINE_2_Y, str_temp2, FONT_SIZE_LINE, white_pixel);
	// Draw the value of temp2
	sd1306_draw_string(sizeof(str_temp2) * 6, OLED_LINE_2_Y, string_data, FONT_SIZE_LINE, white_pixel);
	// Draw the value of temp2
	sd1306_draw_string(sizeof(str_temp2) * 6 + (get_str_size(string_data) + 1) * 6, OLED_LINE_2_Y, "°C", FONT_SIZE_LINE, white_pixel);

	// Convert atm value to string
	ftoa(atm, string_data, 2);

	// Draw a label at line 3
	sd1306_draw_string(OLED_LINE_3_X, OLED_LINE_3_Y, str_atm, FONT_SIZE_LINE, white_pixel);
	// Draw the value of atm
	sd1306_draw_string(sizeof(str_atm) * 6, OLED_LINE_3_Y, string_data, FONT_SIZE_LINE, white_pixel);
	// Draw the units of atm
	sd1306_draw_string(sizeof(str_atm) * 6 + (get_str_size(string_data) + 1) * 6, OLED_LINE_3_Y, "hPa", FONT_SIZE_LINE, white_pixel);

	// Convert altitude value to string
	ftoa(altitude, string_data, 2);

	// Draw a label at line 4
	sd1306_draw_string(OLED_LINE_4_X, OLED_LINE_4_Y, str_altitude, FONT_SIZE_LINE, white_pixel);
	// Draw the value of altitude
	sd1306_draw_string(sizeof(str_altitude) * 6, OLED_LINE_4_Y, string_data, FONT_SIZE_LINE, white_pixel);
	// Draw the units of altitude
	sd1306_draw_string(sizeof(str_altitude) * 6 + (get_str_size(string_data) + 1) * 6, OLED_LINE_4_Y, "m", FONT_SIZE_LINE, white_pixel);

	// Send the buffer to OLED RAM
	sd1306_refresh();
}

/**
  * @brief  Template to show other variables curently not available
  * @param  x: var 1
  * @param  y: var 2
  * @param  z: var 3
  * @retval None.
  */
void update_other(float x, float y, float z)
{
	uint32_t i;
	uint8_t string_data[10];

	// Strings for labels
	uint8_t str_light[] = "Light:";
	uint8_t str_tbd1[] = "TBD 1:";
	uint8_t str_tbd2[] = "TBD 2:";

	// Clear OLED buffer
	clear_oled_buffer();

	// Draw the title
	sd1306_draw_string(OLED_TITLE_X, OLED_TITLE_Y, "   Other", FONT_SIZE_TITLE, white_pixel);

	// Convert x value to string
	ftoa(x, string_data, 2);

	// Draw a label at line 1
	sd1306_draw_string(OLED_LINE_1_X, OLED_LINE_1_Y, str_light, FONT_SIZE_LINE, white_pixel);
	// Draw the value of x
	sd1306_draw_string(sizeof(str_light) * 6, OLED_LINE_1_Y, string_data, FONT_SIZE_LINE, white_pixel);
	// Draw the units of x
	sd1306_draw_string(sizeof(str_light) * 6 + (get_str_size(string_data) + 1) * 6, OLED_LINE_1_Y, "Lux", FONT_SIZE_LINE, white_pixel);

	// Convert y value to string
	ftoa(y, string_data, 2);

	// Draw a label at line 2
	sd1306_draw_string(OLED_LINE_2_X, OLED_LINE_2_Y, str_tbd1, FONT_SIZE_LINE, white_pixel);
	// Draw the value of y
	sd1306_draw_string(sizeof(str_tbd1) * 6, OLED_LINE_2_Y, string_data, FONT_SIZE_LINE, white_pixel);
	// Draw the units of y
	sd1306_draw_string(sizeof(str_tbd1) * 6 + (get_str_size(string_data) + 1) * 6, OLED_LINE_2_Y, "Units", FONT_SIZE_LINE, white_pixel);

	// Convert z value to string
	ftoa(z, string_data, 2);

	// Draw a label at line 3
	sd1306_draw_string(OLED_LINE_3_X, OLED_LINE_3_Y, str_tbd2, FONT_SIZE_LINE, white_pixel);
	// Draw the value of z
	sd1306_draw_string(sizeof(str_tbd2) * 6, OLED_LINE_3_Y, string_data, FONT_SIZE_LINE, white_pixel);
	// Draw the units of z
	sd1306_draw_string(sizeof(str_tbd2) * 6 + (get_str_size(string_data) + 1) * 6, OLED_LINE_3_Y, "Units", FONT_SIZE_LINE, white_pixel);

	// Send the buffer to OLED RAM
	sd1306_refresh();
}

/**
  * @brief  Template to show a logo
  * @param  None.
  * @retval None.
  */
void oled_draw_logo(void)
{
	// Copy image_avnet to OLED buffer
	sd1306_draw_img(Image_avnet_bmp);

	// Send the buffer to OLED RAM
	sd1306_refresh();
}

// reverses a string 'str' of length 'len'
static void reverse(uint8_t *str, int32_t len)
{
	int32_t i = 0;
	int32_t j = len - 1;
	int32_t temp;

	while (i < j)
	{
		temp = str[i];
		str[i] = str[j];
		str[j] = temp;
		i++; j--;
	}
}

/**
  * @brief  Converts a given integer x to string uint8_t[]
  * @param  x: x integer input
  * @param  str: uint8_t array output
  * @param  d: Number of zeros added
  * @retval i: number of digits
  */
int32_t intToStr(int32_t x, uint8_t str[], int32_t d)
{
	int32_t i = 0;
	uint8_t flag_neg = 0;

	if (x < 0)
	{
		flag_neg = 1;
		x *= -1;
	}
	while (x)
	{
		str[i++] = (x % 10) + '0';
		x = x / 10;
	}

	// If number of digits required is more, then
	// add 0s at the beginning
	while (i < d)
	{
		str[i++] = '0';
	}

	if (flag_neg)
	{
		str[i] = '-';
		i++;
	}

	reverse(str, i);
	str[i] = '\0';
	return i;
}

/**
  * @brief  Converts a given integer x to string uint8_t[]
  * @param  n: float number to convert
  * @param  res:
  * @param  afterpoint:
  * @retval None.
  */
void ftoa(float n, uint8_t *res, int32_t afterpoint)
{
	// Extract integer part
	int32_t ipart = (int32_t)n;

	// Extract floating part
	float fpart = n - (float)ipart;

	int32_t i;

	if (ipart < 0)
	{
		res[0] = '-';
		res++;
		ipart *= -1;
	}

	if (fpart < 0)
	{
		fpart *= -1;

		if (ipart == 0)
		{
			res[0] = '-';
			res++;
		}
	}

	// convert integer part to string
	i = intToStr(ipart, res, 1);

	// check for display option after point
	if (afterpoint != 0)
	{
		res[i] = '.';  // add dot

		// Get the value of fraction part upto given no.
		// of points after dot. The third parameter is needed
		// to handle cases like 233.007
		fpart = fpart * pow(10, afterpoint);

		intToStr((int32_t)fpart, res + i + 1, afterpoint);
	}
}

// AVNET logo

const unsigned char Image_avnet_bmp[BUFFER_SIZE] =
{
	0,  0,  0,  0,  0,  0,  0,  0,  0,  0,  0,  0,  0,  0,  0,  0,
	0,  0,  0,  0,  0,  0,  0,  0,  0,  0,  0,  0,  0,  0,  0,  0,
	0,  0,  0,  0,  0,  0,  0,  0,  0,  0,  0,  0,  0,  0,  0,  0,
	0,  0,  0,  0,  0,  0,  0,  0,  0,  0,  0,  0,  0,  0,  0,  0,
	0,  0,  0,  0,  0,  0,  0,  0,  0,  0,  0,  0,  0,  0,  0,  0,
	0,  0,  0,  0,  0,  0,  0,  0,  0,  0,  0,  0,  0,  0,  0,  0,
	0,  0,  0,  0,  0,  0,  0,  0,  0,  0,  0,  0,  0,  0,  0,  0,
	0,  0,  0,  0,  0,  0,  0,  0,  0,  0,  0,  0,  0,  0,  0,  0,
	0,  0,  0,  0,  0,  0,  0,  0,  0,  0,  0,  0,  0,  0,  0,  0,
	0,  0,  0,  0,  0,  0,  0,  0,  0,  0,  0,  0,  0,  0,  0,  0,
	0,  0,  0,  0,  0,  0,  0,  0,  0,  0,  0,  0,  0,  0,  0,  0,
	0,  0,  0,  0,  0,  0,  0,  0,  0,  0,  0,  0,  0,  0,  0,  0,
	0,  0,  0,  0,  0,  0,  0,  0,  0,  0,  0,  0,  0,  0,  0,  0,
	0,  0,  0,  0,  0,  0,  0,  0,  0,  0,  0,  0,  0,  0,  0,  0,
	0,  0,  0,  0,  0,  0,  0,  0,  0,  0,  0,  0,  0,  0,  0,  0,
	0,  0,  0,  0,  0,  0,  0,  0,  0,  0,  0,  0,  0,  0,  0,  0,
	0,  0,  0,  0,  0,  0,  0,128,240,240,240,240, 48,  0,  0,112,
  240,240,240,224,  0,  0,  0,  0,  0,  0,  0,  0,  0,  0,  0,112,
  240,240,240,192,  0,  0,  0,  0,  0,  0,  0,  0,  0,224,240,240,
  240, 16,  0,  0,  0,  0,  0,  0,  0,  0,240,240,240,240,224,128,
	0,  0,  0,  0,  0,  0,  0,  0,240,240,240,240,  0,  0,  0,  0,
	0,  0,  0,  0,  0,  0,240,240,240,240,112,112,112,112,112,112,
  112,112,112,112,112,  0,  0,  0,  0,  0,  0,  0,  0,112,112,112,
  112,112,112,112,240,240,240,240,112,112,112,112,112,112,  0,  0,
	0,  0,  0,  0,  0,224,252,255,255,255, 15,  1,  0,  0,  0,  0,
	3, 15,127,255,255,248,128,  0,  0,  0,  0,  0,  0,  0,  0,  0,
	7, 31,255,255,254,240,  0,  0,  0,  0,224,248,255,255,127,  7,
	0,  0,  0,  0,  0,  0,  0,  0,  0,  0,255,255,255,255, 15, 31,
  127,252,248,224,224,128,  0,  0,255,255,255,255,  0,  0,  0,  0,
	0,  0,  0,  0,  0,  0,255,255,255,255,224,224,224,224,224,224,
  224,224,224,224,  0,  0,  0,  0,  0,  0,  0,  0,  0,  0,  0,  0,
	0,  0,  0,  0,255,255,255,255,  0,  0,  0,  0,  0,  0,  0,  0,
	0,  0,128,240,254,255,127, 15,  1,  0,  0,  0,  0,  0,  0,  0,
	0,  0,  0,  3, 31,255,255,252,224,  0,  0,  0,  0,  0,  0,  0,
	0,  0,  0,  7, 63,255,255,248,240,254,255,255, 31,  3,  0,  0,
	0,  0,  0,  0,  0,  0,  0,  0,  0,  0,255,255,255,255,  0,  0,
	0,  1,  3, 15, 15, 63,126,252,255,255,255,255,  0,  0,  0,  0,
	0,  0,  0,  0,  0,  0,255,255,255,255,129,129,129,129,129,129,
  129,129,129,129,128,  0,  0,  0,  0,  0,  0,  0,  0,  0,  0,  0,
	0,  0,  0,  0,255,255,255,255,  0,  0,  0,  0,  0,  0,  0,  0,
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
};


uint8_t get_str_size(uint8_t * str)
{
	uint8_t legth = 0;
	while (*(str) != NULL)
	{
		str++;
		legth++;
	}
	return legth;
}
