pulcher/secureMoodTracker/secure-mt/secure-mt/build_options.h

#pragma once

// Enables I2C read/write debug
#define ENABLE_READ_WRITE_DEBUG

// Defines how quickly the accelerator data is read and reported
#define ACCEL_READ_PERIOD_SECONDS 10
#define ACCEL_READ_PERIOD_NANO_SECONDS 0
