pulcher/secureMoodTracker/secureMoodTracker/azure_iot_utilities.c

#include <azureiot/iothub_device_client_ll.h>
#include <stdlib.h>
#include <stdio.h>
#include <stdarg.h>
#include <time.h>
#include <azureiot/iothub_client_core_common.h>
#include <azureiot/iothub_client_options.h>
#include <azureiot/iothubtransportmqtt.h>
#include <azureiot/iothub.h>
#include <applibs/log.h>
#include "azure_iot_utilities.h"
#include "build_options.h"
#include "connection_strings.h"


// Refer to https://docs.microsoft.com/en-us/azure/iot-hub/iot-hub-device-sdk-c-intro for more
// information on Azure IoT SDK for C

//
// String containing Hostname, Device Id & Device Key in the format:
// "HostName=<host_name>;DeviceId=<device_id>;SharedAccessKey=<device_key>"

// see information on iothub-explorer at http://aka.ms/iothubgetstartedVSCS
//

#include "connection_strings.h"

static const char connectionString[] = "HostName=iotc-ea758c6a-7653-4553-ada5-6ad55b7c229d.azure-devices.net;DeviceId=22d7fc3c-247c-42c8-8923-86990eae1f33;SharedAccessKey=kR2Kfs/ZwuDP1hohd/3l09bN5trf7HrhVg7zk7vSdA4=";

/// <summary>
///     Maximum amount of time to attempt reconnection when the connection to the IoT Hub drops.
/// </summary>
/// <remarks>Time expressed in seconds. A value of 0 means to retry forever.</remarks>
static const size_t retryTimeoutSeconds = 0;

/// <summary>
///     Function invoked to provide the result of the Device Twin reported properties
///     delivery.
/// </summary>
static DeviceTwinDeliveryConfirmationFnType deviceTwinConfirmationCb = 0;

/// <summary>
///     Function invoked whenever a Direct Method call is received from the IoT Hub.
/// </summary>
static DirectMethodCallFnType directMethodCallCb = 0;

/// <summary>
///     Function invoked whenever a Device Twin update is received from the IoT Hub.
/// </summary>
static TwinUpdateFnType twinUpdateCb = 0;

/// <summary>
///     Function invoked whenever the connection status to the IoT Hub changes.
/// </summary>
static ConnectionStatusFnType hubConnectionStatusCb = 0;

/// <summary>
///     Function invoked whenever a message is received from the IoT Hub.
/// </summary>
static MessageReceivedFnType messageReceivedCb = 0;

/// <summary>
///     Function invoked to report the delivery confirmation of a message sent to the IoT
///     Hub.
/// </summary>
static MessageDeliveryConfirmationFnType messageDeliveryConfirmationCb = 0;

/// <summary>
///     The handle to the IoT Hub client used for communication with the hub.
/// </summary>
IOTHUB_DEVICE_CLIENT_LL_HANDLE iothubClientHandle = NULL;

/// <summary>
///     Used to set the keepalive period over MQTT to 20 seconds.
/// </summary>
static int keepalivePeriodSeconds = 20;

/// <summary>
///     Set of bundle of root certificate authorities.
/// </summary>
static const char azureIoTCertificatesX[] =
    /* DigiCert Baltimore Root */
    "-----BEGIN CERTIFICATE-----\r\n"
    "MIIDdzCCAl+gAwIBAgIEAgAAuTANBgkqhkiG9w0BAQUFADBaMQswCQYDVQQGEwJJ\r\n"
    "RTESMBAGA1UEChMJQmFsdGltb3JlMRMwEQYDVQQLEwpDeWJlclRydXN0MSIwIAYD\r\n"
    "VQQDExlCYWx0aW1vcmUgQ3liZXJUcnVzdCBSb290MB4XDTAwMDUxMjE4NDYwMFoX\r\n"
    "DTI1MDUxMjIzNTkwMFowWjELMAkGA1UEBhMCSUUxEjAQBgNVBAoTCUJhbHRpbW9y\r\n"
    "ZTETMBEGA1UECxMKQ3liZXJUcnVzdDEiMCAGA1UEAxMZQmFsdGltb3JlIEN5YmVy\r\n"
    "VHJ1c3QgUm9vdDCCASIwDQYJKoZIhvcNAQEBBQADggEPADCCAQoCggEBAKMEuyKr\r\n"
    "mD1X6CZymrV51Cni4eiVgLGw41uOKymaZN+hXe2wCQVt2yguzmKiYv60iNoS6zjr\r\n"
    "IZ3AQSsBUnuId9Mcj8e6uYi1agnnc+gRQKfRzMpijS3ljwumUNKoUMMo6vWrJYeK\r\n"
    "mpYcqWe4PwzV9/lSEy/CG9VwcPCPwBLKBsua4dnKM3p31vjsufFoREJIE9LAwqSu\r\n"
    "XmD+tqYF/LTdB1kC1FkYmGP1pWPgkAx9XbIGevOF6uvUA65ehD5f/xXtabz5OTZy\r\n"
    "dc93Uk3zyZAsuT3lySNTPx8kmCFcB5kpvcY67Oduhjprl3RjM71oGDHweI12v/ye\r\n"
    "jl0qhqdNkNwnGjkCAwEAAaNFMEMwHQYDVR0OBBYEFOWdWTCCR1jMrPoIVDaGezq1\r\n"
    "BE3wMBIGA1UdEwEB/wQIMAYBAf8CAQMwDgYDVR0PAQH/BAQDAgEGMA0GCSqGSIb3\r\n"
    "DQEBBQUAA4IBAQCFDF2O5G9RaEIFoN27TyclhAO992T9Ldcw46QQF+vaKSm2eT92\r\n"
    "9hkTI7gQCvlYpNRhcL0EYWoSihfVCr3FvDB81ukMJY2GQE/szKN+OMY3EU/t3Wgx\r\n"
    "jkzSswF07r51XgdIGn9w/xZchMB5hbgF/X++ZRGjD8ACtPhSNzkE1akxehi/oCr0\r\n"
    "Epn3o0WC4zxe9Z2etciefC7IpJ5OCBRLbf1wbWsaY71k5h+3zvDyny67G7fyUIhz\r\n"
    "ksLi4xaNmjICq44Y3ekQEe5+NauQrz4wlHrQMz2nZQ/1/I6eYs9HRCwBXbsdtTLS\r\n"
    "R9I4LtD+gdwyah617jzV/OeBHRnDJELqYzmp\r\n"
    "-----END CERTIFICATE-----\r\n"
    /* DigiCert Global Root CA */
    "-----BEGIN CERTIFICATE-----\r\n"
    "MIIDrzCCApegAwIBAgIQCDvgVpBCRrGhdWrJWZHHSjANBgkqhkiG9w0BAQUFADBh\r\n"
    "MQswCQYDVQQGEwJVUzEVMBMGA1UEChMMRGlnaUNlcnQgSW5jMRkwFwYDVQQLExB3\r\n"
    "d3cuZGlnaWNlcnQuY29tMSAwHgYDVQQDExdEaWdpQ2VydCBHbG9iYWwgUm9vdCBD\r\n"
    "QTAeFw0wNjExMTAwMDAwMDBaFw0zMTExMTAwMDAwMDBaMGExCzAJBgNVBAYTAlVT\r\n"
    "MRUwEwYDVQQKEwxEaWdpQ2VydCBJbmMxGTAXBgNVBAsTEHd3dy5kaWdpY2VydC5j\r\n"
    "b20xIDAeBgNVBAMTF0RpZ2lDZXJ0IEdsb2JhbCBSb290IENBMIIBIjANBgkqhkiG\r\n"
    "9w0BAQEFAAOCAQ8AMIIBCgKCAQEA4jvhEXLeqKTTo1eqUKKPC3eQyaKl7hLOllsB\r\n"
    "CSDMAZOnTjC3U/dDxGkAV53ijSLdhwZAAIEJzs4bg7/fzTtxRuLWZscFs3YnFo97\r\n"
    "nh6Vfe63SKMI2tavegw5BmV/Sl0fvBf4q77uKNd0f3p4mVmFaG5cIzJLv07A6Fpt\r\n"
    "43C/dxC//AH2hdmoRBBYMql1GNXRor5H4idq9Joz+EkIYIvUX7Q6hL+hqkpMfT7P\r\n"
    "T19sdl6gSzeRntwi5m3OFBqOasv+zbMUZBfHWymeMr/y7vrTC0LUq7dBMtoM1O/4\r\n"
    "gdW7jVg/tRvoSSiicNoxBN33shbyTApOB6jtSj1etX+jkMOvJwIDAQABo2MwYTAO\r\n"
    "BgNVHQ8BAf8EBAMCAYYwDwYDVR0TAQH/BAUwAwEB/zAdBgNVHQ4EFgQUA95QNVbR\r\n"
    "TLtm8KPiGxvDl7I90VUwHwYDVR0jBBgwFoAUA95QNVbRTLtm8KPiGxvDl7I90VUw\r\n"
    "DQYJKoZIhvcNAQEFBQADggEBAMucN6pIExIK+t1EnE9SsPTfrgT1eXkIoyQY/Esr\r\n"
    "hMAtudXH/vTBH1jLuG2cenTnmCmrEbXjcKChzUyImZOMkXDiqw8cvpOp/2PV5Adg\r\n"
    "06O/nVsJ8dWO41P0jmP6P6fbtGbfYmbW0W5BjfIttep3Sp+dWOIrWcBAI+0tKIJF\r\n"
    "PnlUkiaY4IBIqDfv8NZ5YBberOgOzW6sRBc4L0na4UU+Krk2U886UAb3LujEV0ls\r\n"
    "YSEY1QSteDwsOoBrp+uvFRTp2InBuThs4pFsiv9kuXclVzDAGySj4dzp30d8tbQk\r\n"
    "CAUw7C29C79Fv1C5qfPrmAESrciIxpg0X40KPMbp1ZWVbd4=\r\n"
    "-----END CERTIFICATE-----\r\n"
    /* D-TRUST Root Class 3 CA 2 2009 */
    "-----BEGIN CERTIFICATE-----\r\n"
    "MIIEMzCCAxugAwIBAgIDCYPzMA0GCSqGSIb3DQEBCwUAME0xCzAJBgNVBAYTAkRF\r\n"
    "MRUwEwYDVQQKDAxELVRydXN0IEdtYkgxJzAlBgNVBAMMHkQtVFJVU1QgUm9vdCBD\r\n"
    "bGFzcyAzIENBIDIgMjAwOTAeFw0wOTExMDUwODM1NThaFw0yOTExMDUwODM1NTha\r\n"
    "ME0xCzAJBgNVBAYTAkRFMRUwEwYDVQQKDAxELVRydXN0IEdtYkgxJzAlBgNVBAMM\r\n"
    "HkQtVFJVU1QgUm9vdCBDbGFzcyAzIENBIDIgMjAwOTCCASIwDQYJKoZIhvcNAQEB\r\n"
    "BQADggEPADCCAQoCggEBANOySs96R+91myP6Oi/WUEWJNTrGa9v+2wBoqOADER03\r\n"
    "UAifTUpolDWzU9GUY6cgVq/eUXjsKj3zSEhQPgrfRlWLJ23DEE0NkVJD2IfgXU42\r\n"
    "tSHKXzlABF9bfsyjxiupQB7ZNoTWSPOSHjRGICTBpFGOShrvUD9pXRl/RcPHAY9R\r\n"
    "ySPocq60vFYJfxLLHLGvKZAKyVXMD9O0Gu1HNVpK7ZxzBCHQqr0ME7UAyiZsxGsM\r\n"
    "lFqVlNpQmvH/pStmMaTJOKDfHR+4CS7zp+hnUquVH+BGPtikw8paxTGA6Eian5Rp\r\n"
    "/hnd2HN8gcqW3o7tszIFZYQ05ub9VxC1X3a/L7AQDcUCAwEAAaOCARowggEWMA8G\r\n"
    "A1UdEwEB/wQFMAMBAf8wHQYDVR0OBBYEFP3aFMSfMN4hvR5COfyrYyNJ4PGEMA4G\r\n"
    "A1UdDwEB/wQEAwIBBjCB0wYDVR0fBIHLMIHIMIGAoH6gfIZ6bGRhcDovL2RpcmVj\r\n"
    "dG9yeS5kLXRydXN0Lm5ldC9DTj1ELVRSVVNUJTIwUm9vdCUyMENsYXNzJTIwMyUy\r\n"
    "MENBJTIwMiUyMDIwMDksTz1ELVRydXN0JTIwR21iSCxDPURFP2NlcnRpZmljYXRl\r\n"
    "cmV2b2NhdGlvbmxpc3QwQ6BBoD+GPWh0dHA6Ly93d3cuZC10cnVzdC5uZXQvY3Js\r\n"
    "L2QtdHJ1c3Rfcm9vdF9jbGFzc18zX2NhXzJfMjAwOS5jcmwwDQYJKoZIhvcNAQEL\r\n"
    "BQADggEBAH+X2zDI36ScfSF6gHDOFBJpiBSVYEQBrLLpME+bUMJm2H6NMLVwMeni\r\n"
    "acfzcNsgFYbQDfC+rAF1hM5+n02/t2A7nPPKHeJeaNijnZflQGDSNiH+0LS4F9p0\r\n"
    "o3/U37CYAqxva2ssJSRyoWXuJVrl5jLn8t+rSfrzkGkj2wTZ51xY/GXUl77M/C4K\r\n"
    "zCUqNQT4YJEVdT1B/yMfGchs64JTBKbkTCJNjYy6zltz7GRUUG3RnFX7acM2w4y8\r\n"
    "PIWmawomDeCTmGCufsYkl4phX5GOZpIJhzbNi5stPvZR1FDUWSi9g/LMKHtThm3Y\r\n"
    "Johw1+qRzT65ysCQblrGXnRl11z+o+I=\r\n"
    "-----END CERTIFICATE-----\r\n";

// Forward declarations.
static void sendMessageCallback(IOTHUB_CLIENT_CONFIRMATION_RESULT result, void *context);
static IOTHUBMESSAGE_DISPOSITION_RESULT receiveMessageCallback(IOTHUB_MESSAGE_HANDLE message,
                                                               void *context);
static void twinCallback(DEVICE_TWIN_UPDATE_STATE updateState, const unsigned char *payLoad,
                         size_t size, void *userContextCallback);
static int directMethodCallback(const char *methodName, const unsigned char *payload, size_t size,
                                unsigned char **response, size_t *response_size,
                                void *userContextCallback);
static void hubConnectionStatusCallback(IOTHUB_CLIENT_CONNECTION_STATUS result,
                                        IOTHUB_CLIENT_CONNECTION_STATUS_REASON reason,
                                        void *userContextCallback);

#if (defined(IOT_CENTRAL_APPLICATION) || defined(IOT_HUB_APPLICATION))
#define MAXS_SIZE 512
// Verify that the connection string is not too long
_Static_assert(sizeof(connectionString) <= MAXS_SIZE, "Connection string too long");
// Verify tthat the connection string is defined
_Static_assert(sizeof(connectionString) > 1, "Connection string not defined! Define MY_CONNECTION_STRING in connection_strings.h");
#endif

/// <summary>
///     Converts the IoT Hub connection status reason to a string.
/// </summary>
static const char *getReasonString(IOTHUB_CLIENT_CONNECTION_STATUS_REASON reason)
{
    static char *reasonString = "unknown reason";
    switch (reason) {
    case IOTHUB_CLIENT_CONNECTION_EXPIRED_SAS_TOKEN:
        reasonString = "IOTHUB_CLIENT_CONNECTION_EXPIRED_SAS_TOKEN";
        break;
    case IOTHUB_CLIENT_CONNECTION_DEVICE_DISABLED:
        reasonString = "IOTHUB_CLIENT_CONNECTION_DEVICE_DISABLED";
        break;
    case IOTHUB_CLIENT_CONNECTION_BAD_CREDENTIAL:
        reasonString = "IOTHUB_CLIENT_CONNECTION_BAD_CREDENTIAL";
        break;
    case IOTHUB_CLIENT_CONNECTION_RETRY_EXPIRED:
        reasonString = "IOTHUB_CLIENT_CONNECTION_RETRY_EXPIRED";
        break;
    case IOTHUB_CLIENT_CONNECTION_NO_NETWORK:
        reasonString = "IOTHUB_CLIENT_CONNECTION_NO_NETWORK";
        break;
    case IOTHUB_CLIENT_CONNECTION_COMMUNICATION_ERROR:
        reasonString = "IOTHUB_CLIENT_CONNECTION_COMMUNICATION_ERROR";
        break;
    case IOTHUB_CLIENT_CONNECTION_OK:
        reasonString = "IOTHUB_CLIENT_CONNECTION_OK";
        break;
    }
    return reasonString;
}

/// <summary>
///     Log a message related to the Azure IoT Hub client with
///     prefix [Azure IoT Hub client]:"
/// </summary>
/// <param name="message">The format string containing the error to output along with
/// placeholders</param>
/// <param name="...">The list of arguments to populate the format string placeholders</param>
void LogMessage(char *message, ...)
{
    va_list args;
    va_start(args, message);
    Log_Debug("[Azure IoT Hub client] ");
    Log_DebugVarArgs(message, args);
    va_end(args);
}

/// <summary>
///     Sets up the client in order to establish the communication channel to Azure IoT Hub.
///
///     The client is created by using the IoT Hub connection string that is provisioned
///     on the device or hardcoded into the source. The client is setup with the following
///     options:
///     - IOTHUB_CLIENT_RETRY_INTERVAL retry policy which, when the network connection
///       to the IoT Hub drops, attempts a reconnection each 5 seconds for a period of time
///       of 5000 seconds before giving up;
///     - MQTT procotol 'keepalive' value of 20 seconds; when no PINGRESP is received after
///       20 seconds, the connection is believed to be down and the retry policy kicks in;
/// </summary>
/// <returns>'true' if the client has been properly set up. 'false' when a fatal error occurred
/// while setting up the client.</returns>
/// <remarks>This function is a no-op when the client has already been set up, i.e. this
/// function has already completed successfully.</remarks>
bool AzureIoT_SetupClient(void)
{
    if (iothubClientHandle != NULL) {
        return true;
    }

    iothubClientHandle =
        IoTHubDeviceClient_LL_CreateFromConnectionString(connectionString, MQTT_Protocol);

    if (iothubClientHandle == NULL) {
        return false;
    }

    if (IoTHubDeviceClient_LL_SetOption(iothubClientHandle, "TrustedCerts",
                                        azureIoTCertificatesX) != IOTHUB_CLIENT_OK) {
        LogMessage("ERROR: failure to set option \"TrustedCerts\"\n");
        return false;
    }

    if (IoTHubDeviceClient_LL_SetOption(iothubClientHandle, OPTION_KEEP_ALIVE,
                                        &keepalivePeriodSeconds) != IOTHUB_CLIENT_OK) {
        LogMessage("ERROR: failure setting option \"%s\"\n", OPTION_KEEP_ALIVE);
        return false;
    }

    // Set callbacks for Message, MethodCall and Device Twin features.
    IoTHubDeviceClient_LL_SetMessageCallback(iothubClientHandle, receiveMessageCallback, NULL);
    IoTHubDeviceClient_LL_SetDeviceMethodCallback(iothubClientHandle, directMethodCallback, NULL);
    IoTHubDeviceClient_LL_SetDeviceTwinCallback(iothubClientHandle, twinCallback, NULL);

    // Set callbacks for connection status related events.
    if (IoTHubDeviceClient_LL_SetConnectionStatusCallback(
            iothubClientHandle, hubConnectionStatusCallback, NULL) != IOTHUB_CLIENT_OK) {
        LogMessage("ERROR: failure setting callback\n");
        return false;
    }

    // Set retry policy for the connection to the IoT Hub.
    if (IoTHubDeviceClient_LL_SetRetryPolicy(iothubClientHandle, IOTHUB_CLIENT_RETRY_INTERVAL,
                                             retryTimeoutSeconds) != IOTHUB_CLIENT_OK) {
        LogMessage("ERROR: failure setting retry policy\n");
        return false;
    }

    return true;
}

/// <summary>
///     Destroys the Azure IoT Hub client.
/// </summary>
void AzureIoT_DestroyClient(void)
{
    if (iothubClientHandle != NULL) {
        IoTHubDeviceClient_LL_Destroy(iothubClientHandle);
        iothubClientHandle = NULL;
    }
}

/// <summary>
///     Periodically outputs a provided format string with a variable number of arguments.
/// </summary>
/// <param name="lastInvokedTime">Pointer where to store the 'last time this function has been
/// invoked' information</param>
/// <param name="periodInSeconds">The desired period of the output</param>
/// <param name="format">The format string</param>
static void PeriodicLogVarArgs(time_t *lastInvokedTime, time_t periodInSeconds, const char *format,
                               ...)
{
    struct timespec ts;
    int timeOk = timespec_get(&ts, TIME_UTC);
    if (!timeOk) {
        return;
    }

    if (ts.tv_sec > *lastInvokedTime + periodInSeconds) {
        va_list args;
        va_start(args, format);
        Log_Debug("[Azure IoT Hub client] ");
        Log_DebugVarArgs(format, args);
        va_end(args);
        *lastInvokedTime = ts.tv_sec;
    }
}

/// <summary>
///     Keeps IoT Hub Client alive by exchanging data with the Azure IoT Hub.
/// </summary>
/// <remarks>
///     This function must to be invoked periodically so that the Azure IoT Hub
///     SDK can accomplish its work (e.g. sending messages, invocation of callbacks, reconnection
///     attempts, and so forth).
/// </remarks>
void AzureIoT_DoPeriodicTasks(void)
{
    static time_t lastTimeLogged = 0;
    PeriodicLogVarArgs(&lastTimeLogged, 5, "INFO: %s calls in progress...\n", __func__);

    // DoWork - send some of the buffered events to the IoT Hub, and receive some of the buffered
    // events from the IoT Hub.
    IoTHubDeviceClient_LL_DoWork(iothubClientHandle);
}

/// <summary>
///     Creates and enqueues a message to be delivered the IoT Hub. The message is not actually sent
///     immediately, but it is sent on the next invocation of AzureIoT_DoPeriodicTasks().
/// </summary>
/// <param name="messagePayload">The payload of the message to send.</param>
void AzureIoT_SendMessage(const char *messagePayload)
{
    if (iothubClientHandle == NULL) {
        LogMessage("WARNING: IoT Hub client not initialized\n");
        return;
    }

    IOTHUB_MESSAGE_HANDLE messageHandle = IoTHubMessage_CreateFromString(messagePayload);

    if (messageHandle == 0) {
        LogMessage("WARNING: unable to create a new IoTHubMessage\n");
        return;
    }

    if (IoTHubDeviceClient_LL_SendEventAsync(iothubClientHandle, messageHandle, sendMessageCallback,
                                             /*&callback_param*/ 0) != IOTHUB_CLIENT_OK) {
        LogMessage("WARNING: failed to hand over the message to IoTHubClient\n");
    } else {
        LogMessage("INFO: IoTHubClient accepted the message for delivery\n");
    }

    IoTHubMessage_Destroy(messageHandle);
}

/// <summary>
///     Sets the function to be invoked whenever the Device Twin properties have been delivered to
///     the IoT Hub.
/// </summary>
/// <param name="callback">The function pointer to the callback function.</param>
void AzureIoT_SetDeviceTwinDeliveryConfirmationCallback(
    DeviceTwinDeliveryConfirmationFnType callback)
{
    deviceTwinConfirmationCb = callback;
}

/// <summary>
///     Callback invoked when the Device Twin reported properties are accepted by IoT Hub.
/// </summary>
static void reportStatusCallback(int result, void *context)
{
    LogMessage("INFO: Device Twin reported properties update result: HTTP status code %d\n",
               result);
    if (deviceTwinConfirmationCb)
        deviceTwinConfirmationCb(result);
}

/// <summary>
///     Creates and enqueues a report containing the name and value pair of a Device Twin reported
///     property.
///     The report is not actually sent immediately, but it is sent on the next invocation of
///     AzureIoT_DoPeriodicTasks().
/// </summary>
void AzureIoT_TwinReportState(const char *propertyName, size_t propertyValue)
{
    if (iothubClientHandle == NULL) {
        LogMessage("ERROR: client not initialized\n");
        return;
    }

    char *reportedPropertiesString = NULL;
    JSON_Value *reportedPropertiesRootJson = json_value_init_object();
    if (reportedPropertiesRootJson == NULL) {
        LogMessage("ERROR: could not create the JSON_Value for Device Twin reporting.\n");
        return;
    }

    JSON_Object *reportedPropertiesJson = json_value_get_object(reportedPropertiesRootJson);
    if (reportedPropertiesJson == NULL) {
        LogMessage("ERROR: could not get the JSON_Object for Device Twin reporting.\n");
        goto cleanup;
    }

    if (JSONSuccess !=
        json_object_set_number(reportedPropertiesJson, propertyName, propertyValue)) {
        LogMessage("ERROR: could not set the property value for Device Twin reporting.\n");
        goto cleanup;
    }

    reportedPropertiesString = json_serialize_to_string(reportedPropertiesRootJson);
    if (reportedPropertiesString == NULL) {
        LogMessage(
            "ERROR: could not serialize the JSON payload to string for Device "
            "Twin reporting.\n");
        goto cleanup;
    }

    if (IoTHubDeviceClient_LL_SendReportedState(
            iothubClientHandle, (unsigned char *)reportedPropertiesString,
            strlen(reportedPropertiesString), reportStatusCallback, 0) != IOTHUB_CLIENT_OK) {
        LogMessage("ERROR: failed to set reported property '%s'.\n", propertyName);
    } else {
        LogMessage("INFO: Set reported property '%s' to value %d.\n", propertyName, propertyValue);
    }

cleanup:
    if (reportedPropertiesRootJson != NULL) {
        json_value_free(reportedPropertiesRootJson);
    }
    if (reportedPropertiesString != NULL) {
        json_free_serialized_string(reportedPropertiesString);
    }
}

/// <summary>
///     Sets a callback function invoked whenever a message is received from IoT Hub.
/// </summary>
/// <param name="callback">The callback function invoked when a message is received</param>
void AzureIoT_SetMessageReceivedCallback(MessageReceivedFnType callback)
{
    messageReceivedCb = callback;
}

/// <summary>
///     Sets the function to be invoked whenever the message to the Iot Hub has been delivered.
/// </summary>
/// <param name="callback">The function pointer to the callback function.</param>
void AzureIoT_SetMessageConfirmationCallback(MessageDeliveryConfirmationFnType callback)
{
    messageDeliveryConfirmationCb = callback;
}

/// <summary>
///     Function invoked when the message delivery confirmation is being reported.
/// </summary>
/// <param name="result">Message delivery status</param>
/// <param name="context">User specified context</param>
static void sendMessageCallback(IOTHUB_CLIENT_CONFIRMATION_RESULT result, void *context)
{
    LogMessage("INFO: Message received by IoT Hub. Result is: %d\n", result);
    if (messageDeliveryConfirmationCb) {
        messageDeliveryConfirmationCb(result == IOTHUB_CLIENT_CONFIRMATION_OK);
    }
}

/// <summary>
///     Callback function invoked when a message is received from IoT Hub.
/// </summary>
/// <param name="message">The handle of the received message</param>
/// <param name="context">The user context specified at IoTHubDeviceClient_LL_SetMessageCallback()
/// invocation time</param>
/// <returns>Return value to indicates the message procession status (i.e. accepted, rejected,
/// abandoned)</returns>
static IOTHUBMESSAGE_DISPOSITION_RESULT receiveMessageCallback(IOTHUB_MESSAGE_HANDLE message,
                                                               void *context)
{
    const unsigned char *buffer = NULL;
    size_t size = 0;
    if (IoTHubMessage_GetByteArray(message, &buffer, &size) != IOTHUB_MESSAGE_OK) {
        LogMessage("WARNING: failure performing IoTHubMessage_GetByteArray\n");
        return IOTHUBMESSAGE_REJECTED;
    }

    // 'buffer' is not zero terminated.
    unsigned char *str_msg = (unsigned char *)malloc(size + 1);
    if (str_msg == NULL) {
        LogMessage("ERROR: could not allocate buffer for incoming message\n");
        abort();
    }
    memcpy(str_msg, buffer, size);
    str_msg[size] = '\0';

    if (messageReceivedCb != 0) {
        messageReceivedCb(str_msg);
    } else {
        LogMessage("WARNING: no user callback set up for event 'message received from IoT Hub'\n");
    }

    LogMessage("INFO: Received message '%s' from IoT Hub\n", str_msg);
    free(str_msg);

    return IOTHUBMESSAGE_ACCEPTED;
}

/// <summary>
///     Sets the function to be invoked whenever a Direct Method call from the IoT Hub is received.
/// </summary>
/// <param name="callback">The callback function invoked when a Direct Method call is
/// received</param>
void AzureIoT_SetDirectMethodCallback(DirectMethodCallFnType callback)
{
    directMethodCallCb = callback;
}

/// <summary>
///     Sets the function callback invoked whenever a Device Twin update from the IoT Hub is
///     received.
/// </summary>
/// <param name="callback">The callback function invoked when a Device Twin update is
/// received</param>
void AzureIoT_SetDeviceTwinUpdateCallback(TwinUpdateFnType callback)
{
    twinUpdateCb = callback;
}

/// <summary>
///     Callback when direct method is called.
/// </summary>
static int directMethodCallback(const char *methodName, const unsigned char *payload, size_t size,
                                unsigned char **response, size_t *responseSize,
                                void *userContextCallback)
{
    LogMessage("INFO: Trying to invoke method %s\n", methodName);

    int result = 404;

    if (directMethodCallCb != NULL) {
        char *responseFromCallback = NULL;
        size_t responseFromCallbackSize = 0;

        result = directMethodCallCb(methodName, payload, size, &responseFromCallback,
                                    &responseFromCallbackSize);
        *responseSize = responseFromCallbackSize;
        *response = responseFromCallback;
    } else {
        LogMessage("INFO: No method '%s' found, HttpStatus=%d\n", methodName, result);
        static const char methodNotFound[] = "\"No method found\"";
        *responseSize = strlen(methodNotFound);
        *response = (unsigned char *)malloc(*responseSize);
        if (*response != NULL) {
            strncpy((char *)(*response), methodNotFound, *responseSize);
        } else {
            LogMessage("ERROR: Cannot create response message for method call.\n");
            abort();
        }
    }

    return result;
}

/// <summary>
///     Callback invoked when a Device Twin update is received from IoT Hub.
/// </summary>
static void twinCallback(DEVICE_TWIN_UPDATE_STATE updateState, const unsigned char *payLoad,
                         size_t payLoadSize, void *userContextCallback)
{
    size_t nullTerminatedJsonSize = payLoadSize + 1;
    char *nullTerminatedJsonString = (char *)malloc(nullTerminatedJsonSize);
    if (nullTerminatedJsonString == NULL) {
        LogMessage("ERROR: Could not allocate buffer for twin update payload.\n");
        abort();
    }

    // Copy the provided buffer to a null terminated buffer.
    memcpy(nullTerminatedJsonString, payLoad, payLoadSize);
    // Add the null terminator at the end.
    nullTerminatedJsonString[nullTerminatedJsonSize - 1] = 0;

    JSON_Value *rootProperties = NULL;
    rootProperties = json_parse_string(nullTerminatedJsonString);
    if (rootProperties == NULL) {
        LogMessage("WARNING: Cannot parse the string as JSON content.\n");
        goto cleanup;
    }

    JSON_Object *rootObject = json_value_get_object(rootProperties);
    JSON_Object *desiredProperties = json_object_dotget_object(rootObject, "desired");
    if (desiredProperties == NULL) {
        desiredProperties = rootObject;
    }
    // Call the provided Twin Device callback if any.
    if (twinUpdateCb != NULL) {
        twinUpdateCb(desiredProperties);
    }

cleanup:
    // Release the allocated memory.
    json_value_free(rootProperties);
    free(nullTerminatedJsonString);
}

/// <summary>
///     Sets the function to be invoked whenever the connection status to the IoT Hub changes.
/// </summary>
/// <param name="callback">The callback function invoked when Azure IoT Hub network connection
/// status changes.</param>
void AzureIoT_SetConnectionStatusCallback(ConnectionStatusFnType callback)
{
    hubConnectionStatusCb = callback;
}

/// <summary>
///     Callback function invoked whenever the connection status to IoT Hub changes.
/// </summary>
/// <param name="result">Current authentication status</param>
/// <param name="reason">result's specific reason</param>
/// <param name="userContextCallback">User specified context</param>
static void hubConnectionStatusCallback(IOTHUB_CLIENT_CONNECTION_STATUS result,
                                        IOTHUB_CLIENT_CONNECTION_STATUS_REASON reason,
                                        void *userContextCallback)
{
    bool authenticated = (result == IOTHUB_CLIENT_CONNECTION_AUTHENTICATED);
    if (hubConnectionStatusCb) {
        hubConnectionStatusCb(result == IOTHUB_CLIENT_CONNECTION_AUTHENTICATED);
    }
    const char *reasonString = getReasonString(reason);
    if (!authenticated) {
        LogMessage("INFO: IoT Hub connection is down (%s), retrying connection in 5 seconds...\n",
                   reasonString);
    } else {
        LogMessage("INFO: connection to the IoT Hub has been established (%s).\n", reasonString);
    }
}

/// <summary>
///     Initializes the Azure IoT Hub SDK.
/// </summary>
/// <return>'true' if initialization has been successful.</param>
bool AzureIoT_Initialize(void)
{
    if (IoTHub_Init() != 0) {
        LogMessage("ERROR: failed initializing platform.\n");
        return false;
    }
    return true;
}

/// <summary>
///     Deinitializes the Azure IoT Hub SDK.
/// </summary>
void AzureIoT_Deinitialize(void)
{
    IoTHub_Deinit();
}
/// <summary>
///     Creates and enqueues reported properties state using a prepared json string.
///     The report is not actually sent immediately, but it is sent on the next
///     invocation of AzureIoT_DoPeriodicTasks().
/// </summary>
void AzureIoT_TwinReportStateJson(
	char *reportedPropertiesString,
	size_t reportedPropertiesSize)
{

	if (iothubClientHandle == NULL) {
		LogMessage("ERROR: client not initialized\n");
	}
	else {
		if (reportedPropertiesString != NULL) {
			if (IoTHubDeviceClient_LL_SendReportedState(iothubClientHandle,
				(unsigned char *)reportedPropertiesString, reportedPropertiesSize,
				reportStatusCallback, 0) != IOTHUB_CLIENT_OK) {
				LogMessage("ERROR: failed to set reported state as '%s'.\n",
					reportedPropertiesString);
			}
			else {
				LogMessage("INFO: Reported state as '%s'.\n", reportedPropertiesString);
			}
		}
		else {
			LogMessage("ERROR: no JSON string for Device Twin reporting.\n");
		}
	}
}
